karyandrew/hutchfinity/scad/gridfinity/stl/bin-5x7x5h.stl

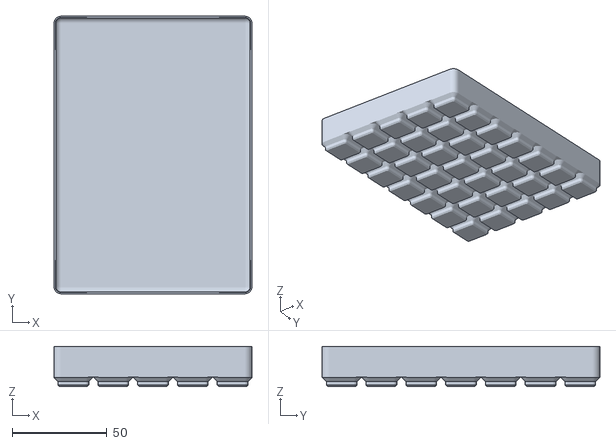
[picture p15: CAD file, 2026-06-07]
scad/gridfinity/stl/bin-5x7x5h.stl
104.5 x 146.5 x 21.2
