karyandrew/hutchfinity/scad/gridfinity/stl/bin-2x10x5h.stl

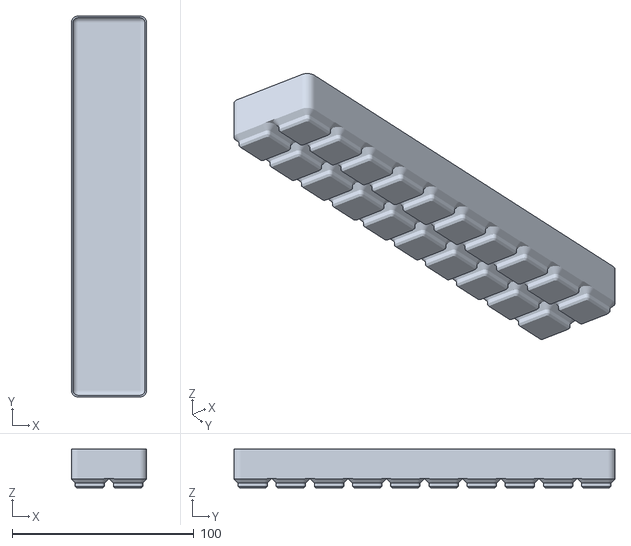
[picture p16: CAD file, 2026-06-07]
scad/gridfinity/stl/bin-2x10x5h.stl
41.5 x 209.5 x 21.2
