karyandrew/hutchfinity/scad/gridfinity/stl/bin-2x8x20h.stl

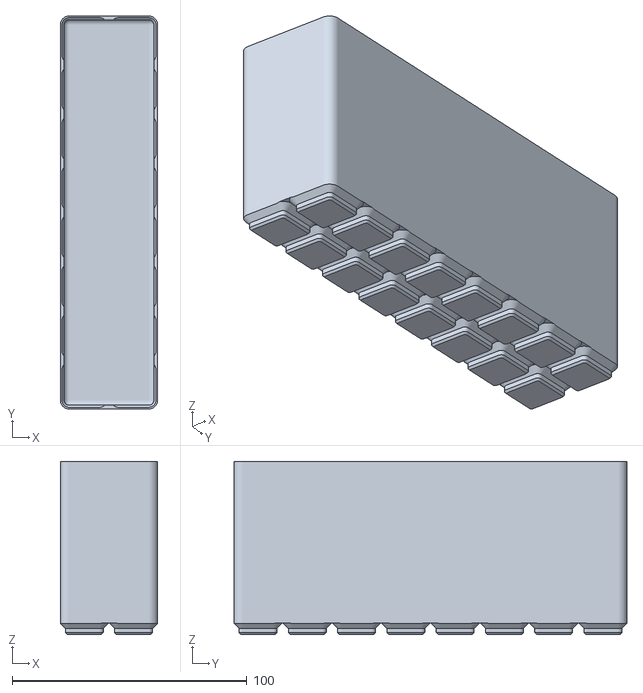
[picture p17: CAD file, 2026-06-07]
scad/gridfinity/stl/bin-2x8x20h.stl
41.5 x 167.5 x 73.7
