karyandrew/hutchfinity/scad/gridfinity/stl/bin-2x3x5h.stl

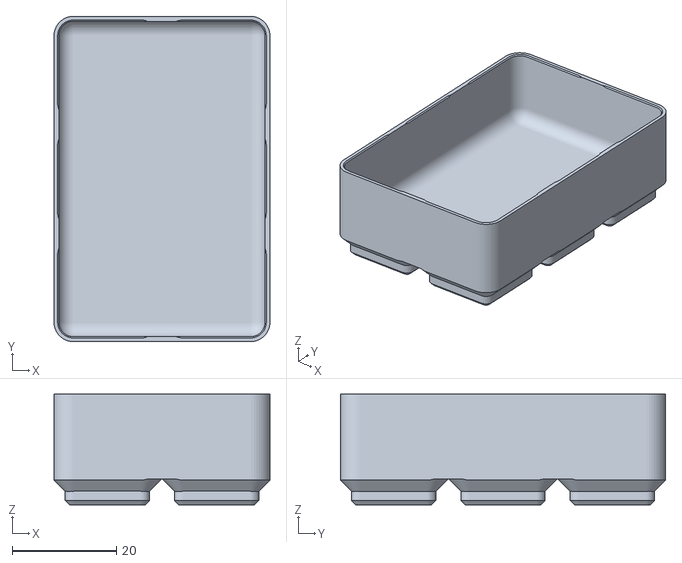
[picture p18: CAD file, 2026-06-07]
scad/gridfinity/stl/bin-2x3x5h.stl
41.5 x 62.5 x 21.2
