karyandrew/hutchfinity/scad/gridfinity/stl/bin-4x8x10h.stl

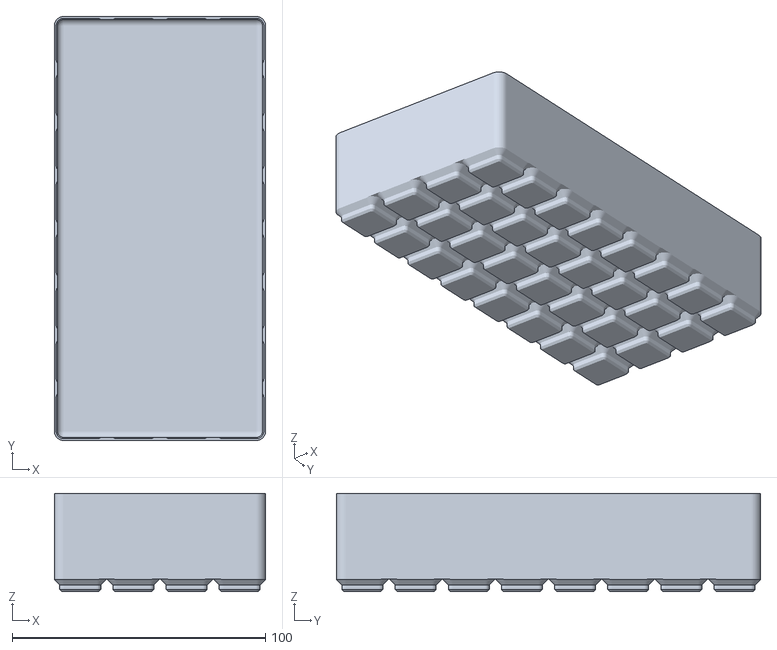
[picture p19: CAD file, 2026-06-07]
scad/gridfinity/stl/bin-4x8x10h.stl
83.5 x 167.5 x 38.7
