karyandrew/hutchfinity/scad/gridfinity/stl/bin-3x10x5h.stl

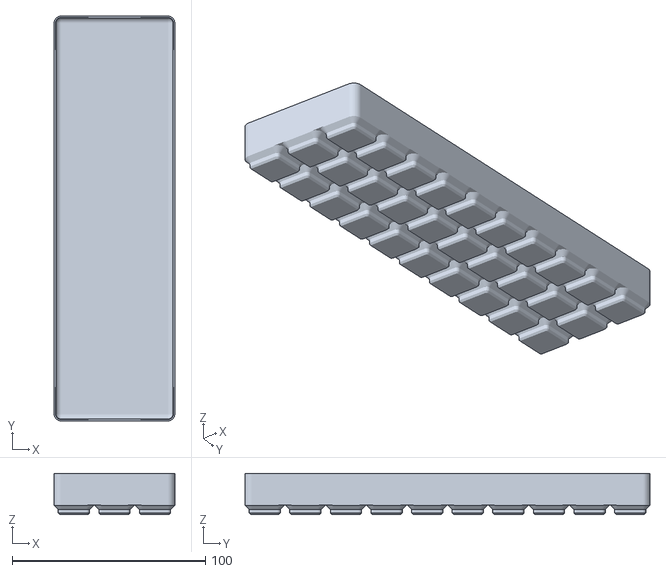
[picture p20: CAD file, 2026-06-07]
scad/gridfinity/stl/bin-3x10x5h.stl
62.5 x 209.5 x 21.2
