karyandrew/hutchfinity/scad/gridfinity/stl/bin-3x7x20h.stl

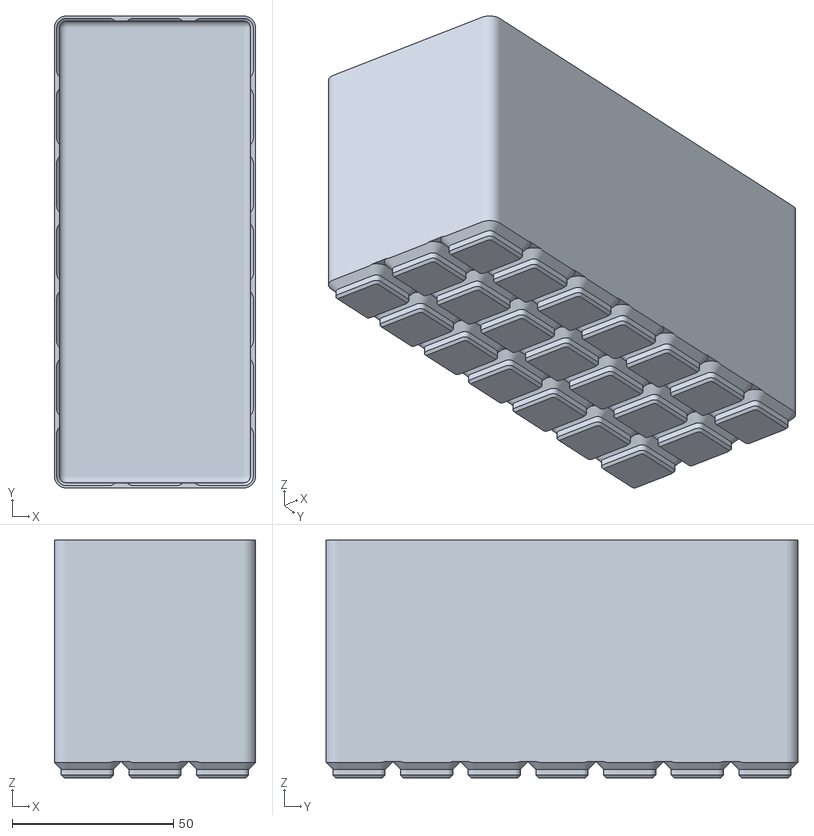
[picture p21: CAD file, 2026-06-07]
scad/gridfinity/stl/bin-3x7x20h.stl
62.5 x 146.5 x 73.7
