karyandrew/hutchfinity/scad/gridfinity/stl/bin-3x7x10h.stl

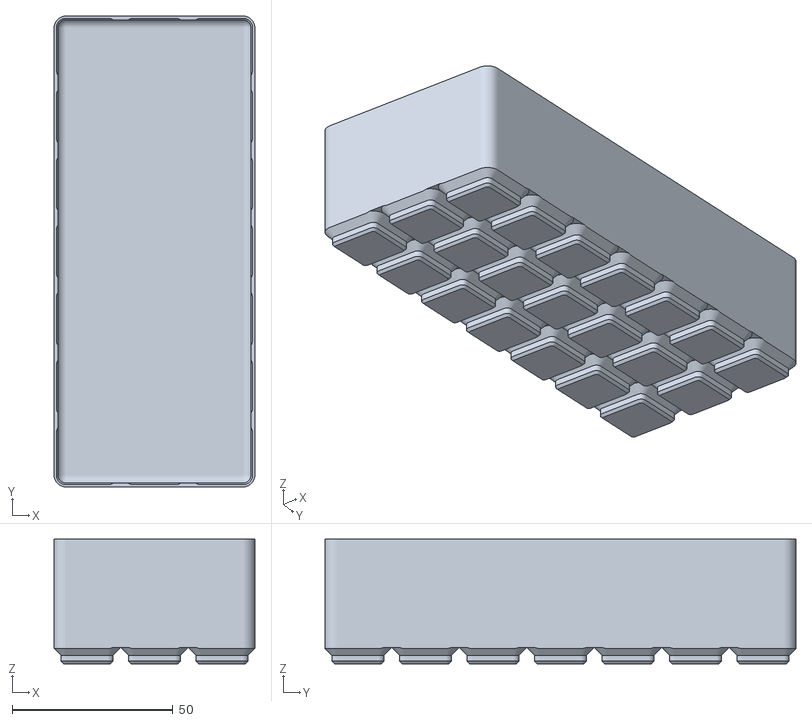
[picture p22: CAD file, 2026-06-07]
scad/gridfinity/stl/bin-3x7x10h.stl
62.5 x 146.5 x 38.7
