karyandrew/hutchfinity/scad/gridfinity/stl/baseplate-regular-cropped.stl

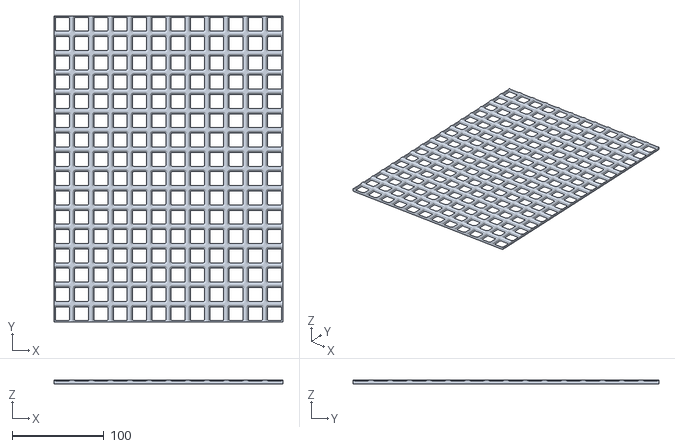
[picture p23: CAD file, 2026-06-07]
scad/gridfinity/stl/baseplate-regular-cropped.stl
249.0 x 333.0 x 4.00
