karyandrew/hutchfinity/scad/gridfinity/stl/tub-mini-10u.stl

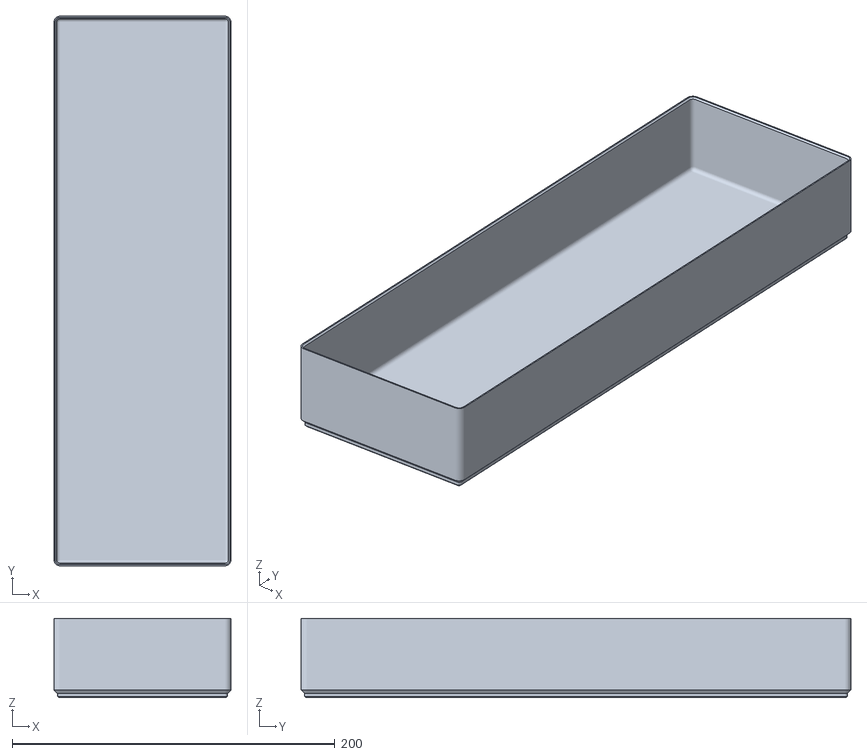
[picture p24: CAD file, 2026-06-07]
scad/gridfinity/stl/tub-mini-10u.stl
109.7 x 340.7 x 49.2
