karyandrew/hutchfinity/scad/gridfinity/stl/bin-3x6x10h.stl

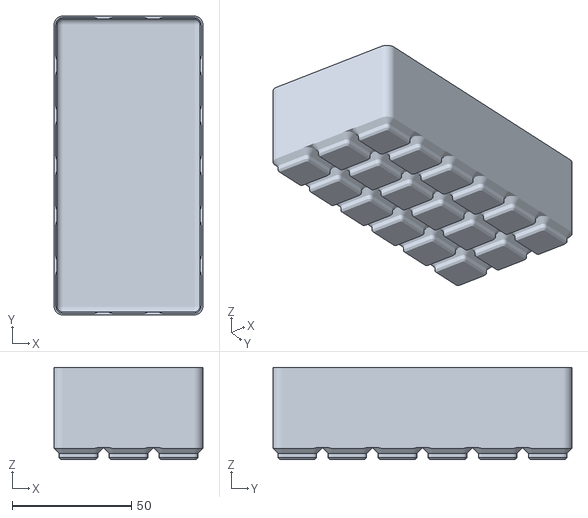
[picture p25: CAD file, 2026-06-07]
scad/gridfinity/stl/bin-3x6x10h.stl
62.5 x 125.5 x 38.7
