karyandrew/hutchfinity/scad/gridfinity/stl/bin-3x4x10h.stl

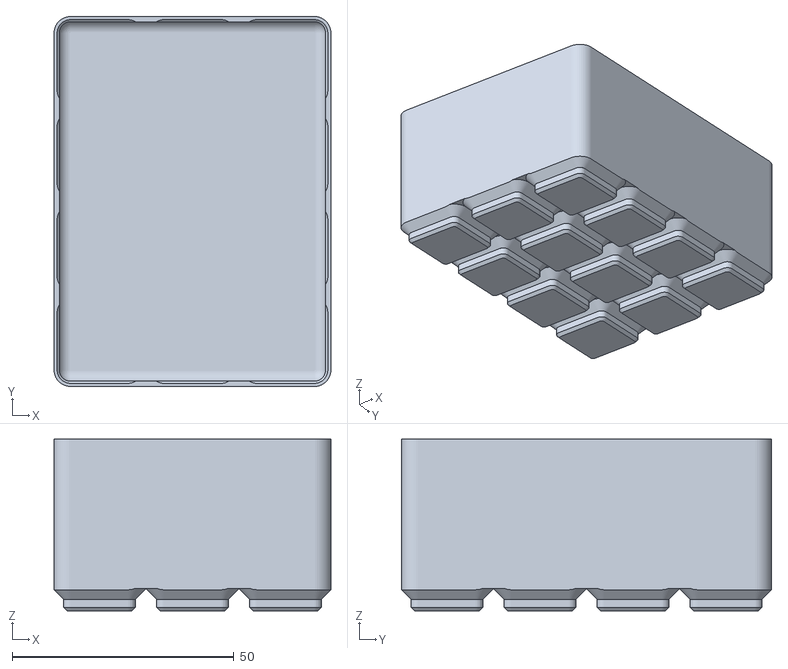
[picture p26: CAD file, 2026-06-07]
scad/gridfinity/stl/bin-3x4x10h.stl
62.5 x 83.5 x 38.7
