karyandrew/hutchfinity/scad/gridfinity/stl/bin-3x5x20h.stl

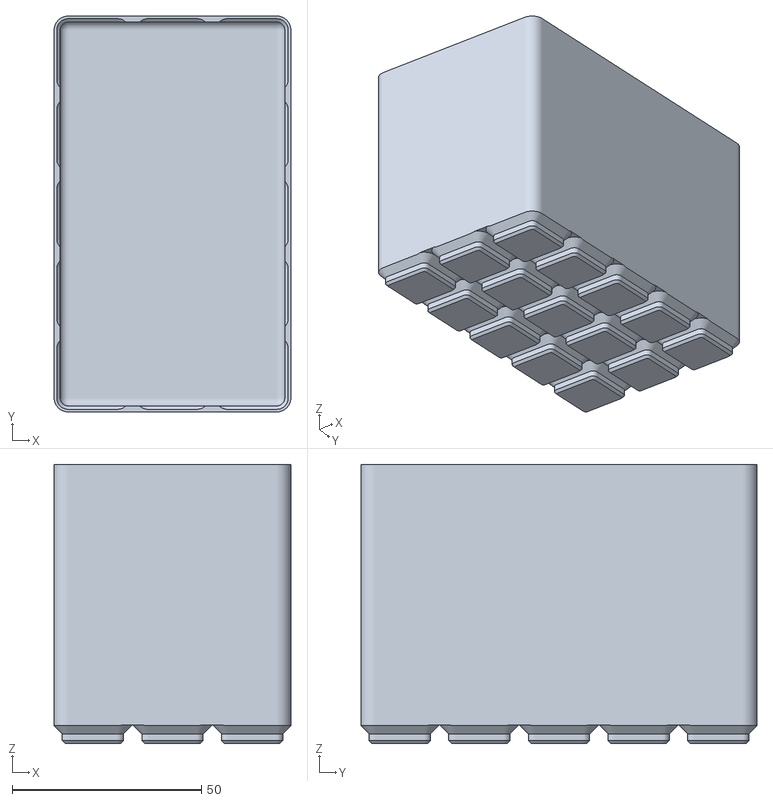
[picture p27: CAD file, 2026-06-07]
scad/gridfinity/stl/bin-3x5x20h.stl
62.5 x 104.5 x 73.7
