karyandrew/hutchfinity/scad/gridfinity/stl/bin-5x10x10h.stl

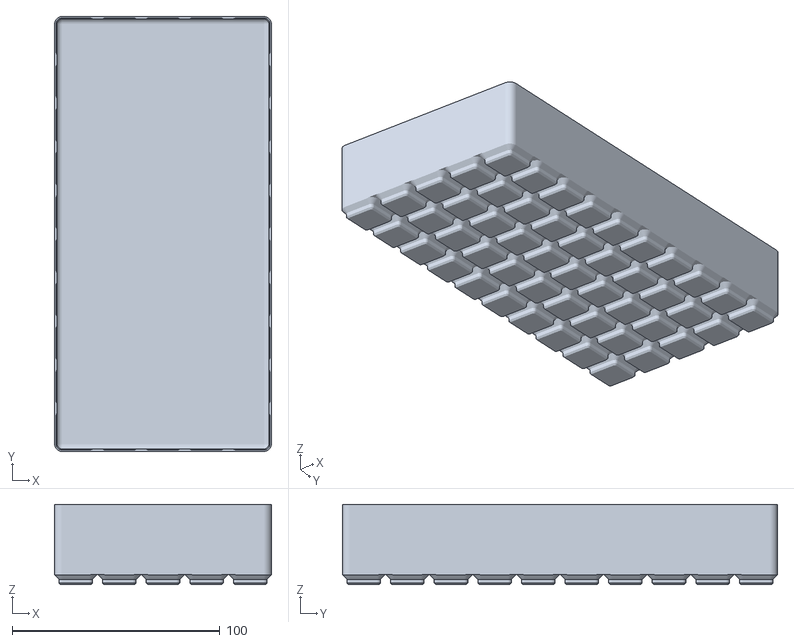
[picture p28: CAD file, 2026-06-07]
scad/gridfinity/stl/bin-5x10x10h.stl
104.5 x 209.5 x 38.7
