karyandrew/hutchfinity/scad/gridfinity/stl/bin-1x8x5h.stl

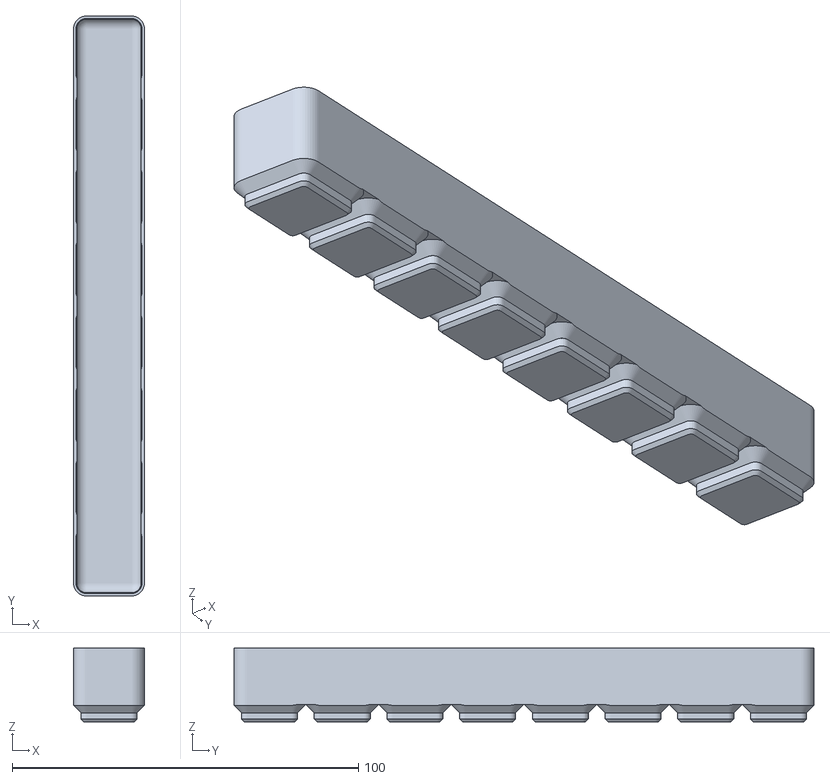
[picture p29: CAD file, 2026-06-07]
scad/gridfinity/stl/bin-1x8x5h.stl
20.5 x 167.5 x 21.2
