karyandrew/hutchfinity/scad/gridfinity/stl/bin-5x8x10h.stl

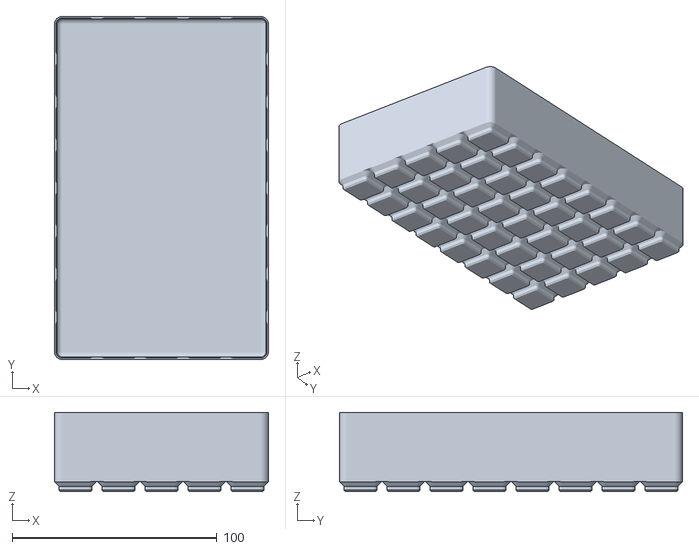
[picture p30: CAD file, 2026-06-07]
scad/gridfinity/stl/bin-5x8x10h.stl
104.5 x 167.5 x 38.7
