karyandrew/hutchfinity/scad/gridfinity/stl/bin-1x9x20h.stl

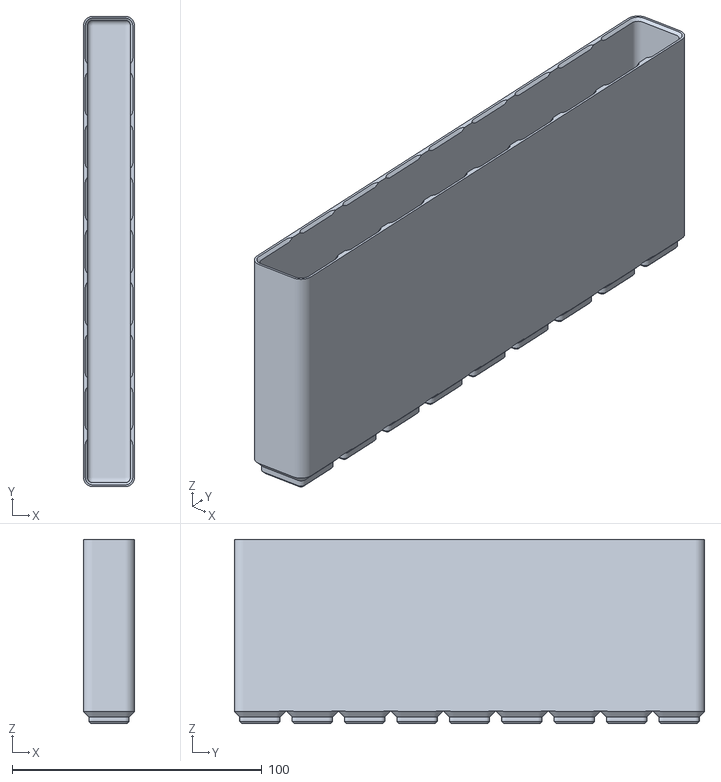
[picture p31: CAD file, 2026-06-07]
scad/gridfinity/stl/bin-1x9x20h.stl
20.5 x 188.5 x 73.7
