karyandrew/hutchfinity/scad/gridfinity/stl/bin-1x10x10h.stl

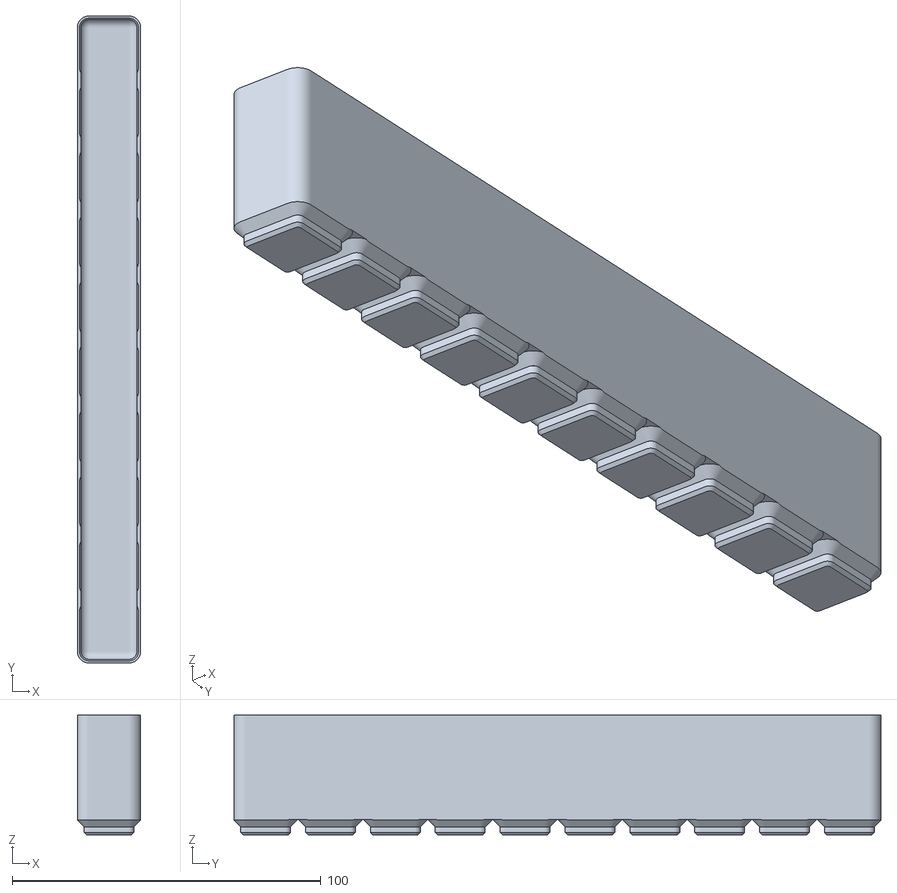
[picture p32: CAD file, 2026-06-07]
scad/gridfinity/stl/bin-1x10x10h.stl
20.5 x 209.5 x 38.7
