karyandrew/hutchfinity/scad/gridfinity/stl/tub-regular-10u.stl

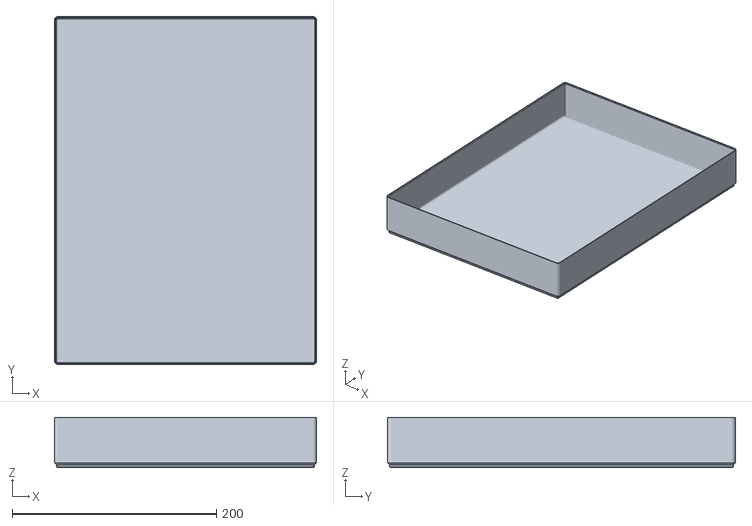
[picture p33: CAD file, 2026-06-07]
scad/gridfinity/stl/tub-regular-10u.stl
256.7 x 340.7 x 49.2
