karyandrew/hutchfinity/scad/gridfinity/stl/bin-5x10x20h.stl

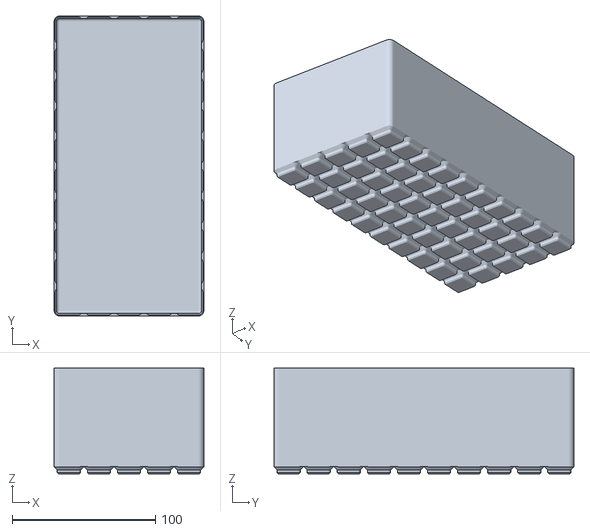
[picture p34: CAD file, 2026-06-07]
scad/gridfinity/stl/bin-5x10x20h.stl
104.5 x 209.5 x 73.7
