karyandrew/hutchfinity/scad/gridfinity/stl/bin-1x6x20h.stl

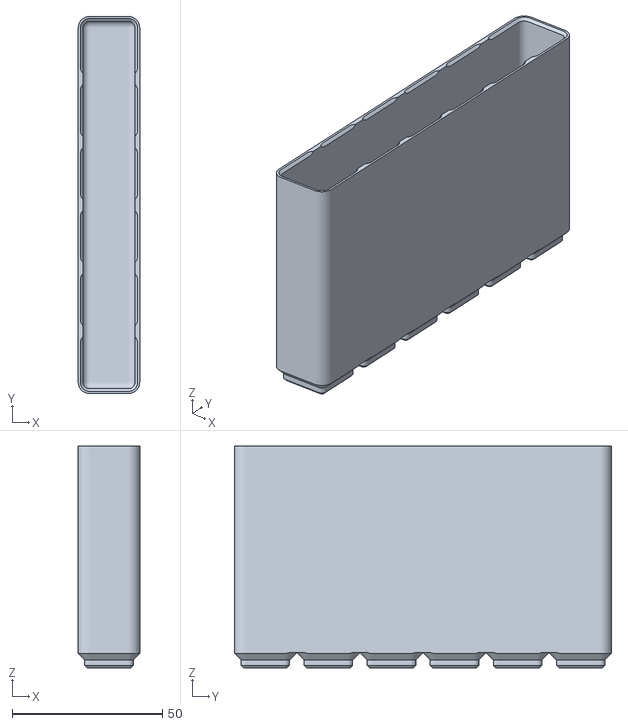
[picture p35: CAD file, 2026-06-07]
scad/gridfinity/stl/bin-1x6x20h.stl
20.5 x 125.5 x 73.7
