karyandrew/hutchfinity/scad/gridfinity/stl/bin-5x8x20h.stl

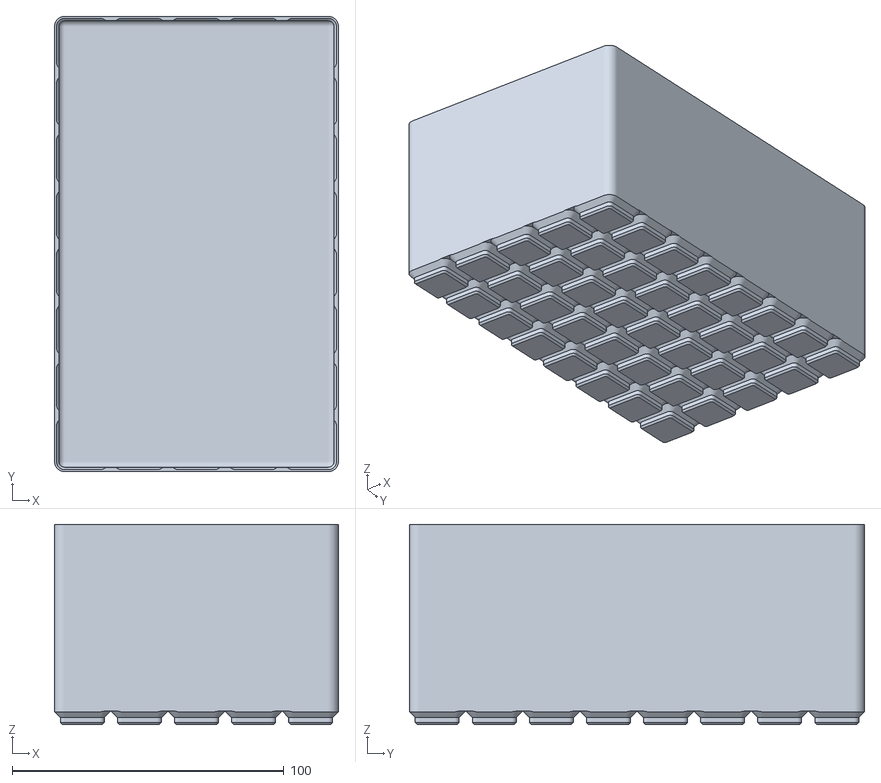
[picture p36: CAD file, 2026-06-07]
scad/gridfinity/stl/bin-5x8x20h.stl
104.5 x 167.5 x 73.7
