karyandrew/hutchfinity/scad/gridfinity/stl/bin-4x10x5h.stl

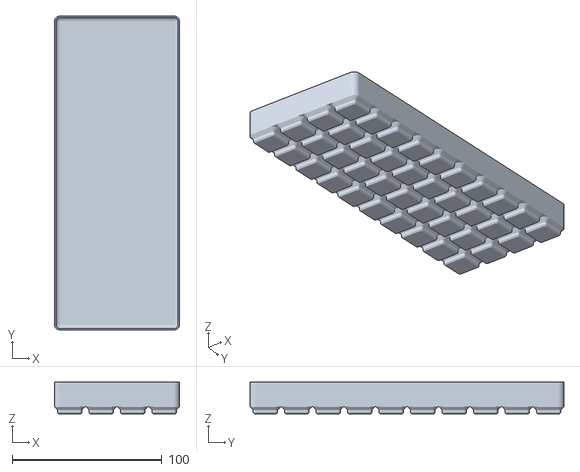
[picture p37: CAD file, 2026-06-07]
scad/gridfinity/stl/bin-4x10x5h.stl
83.5 x 209.5 x 21.2
