karyandrew/hutchfinity/scad/gridfinity/stl/tub-mega-10u.stl

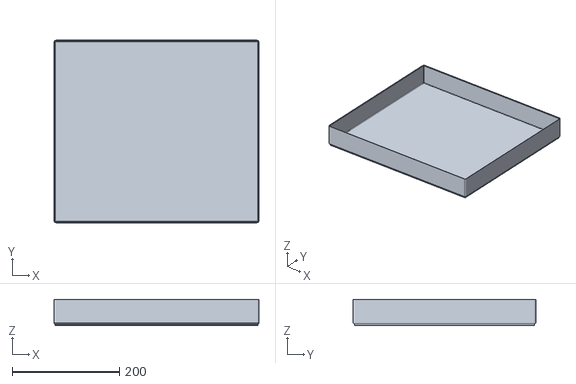
[picture p38: CAD file, 2026-06-07]
scad/gridfinity/stl/tub-mega-10u.stl
382.7 x 340.7 x 49.2
