karyandrew/hutchfinity/scad/gridfinity/stl/bin-2x7x5h.stl

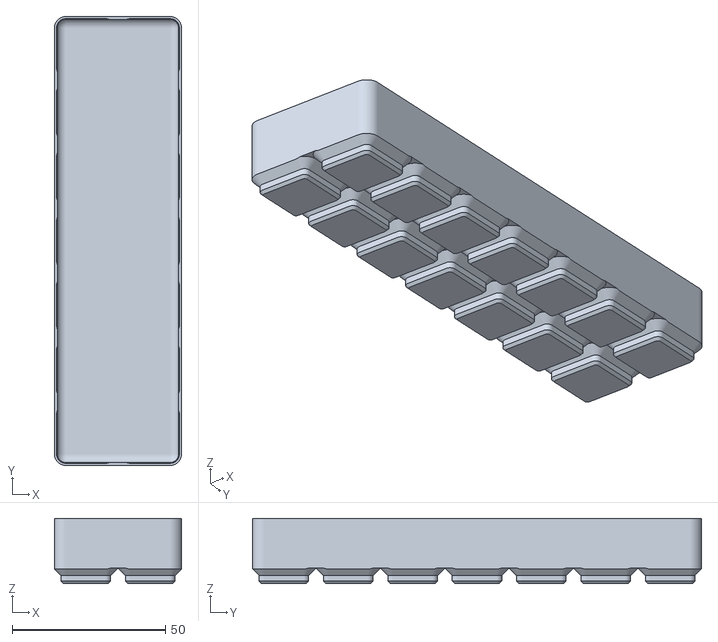
[picture p39: CAD file, 2026-06-07]
scad/gridfinity/stl/bin-2x7x5h.stl
41.5 x 146.5 x 21.2
