karyandrew/hutchfinity/scad/gridfinity/stl/bin-3x4x5h.stl

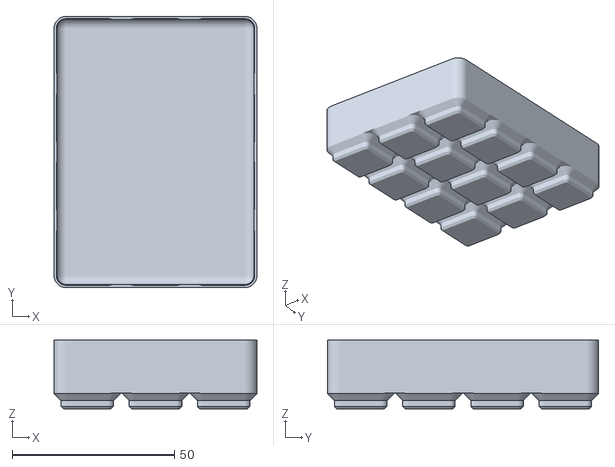
[picture p40: CAD file, 2026-06-07]
scad/gridfinity/stl/bin-3x4x5h.stl
62.5 x 83.5 x 21.2
