karyandrew/hutchfinity/scad/gridfinity/stl/bin-1x6x10h.stl

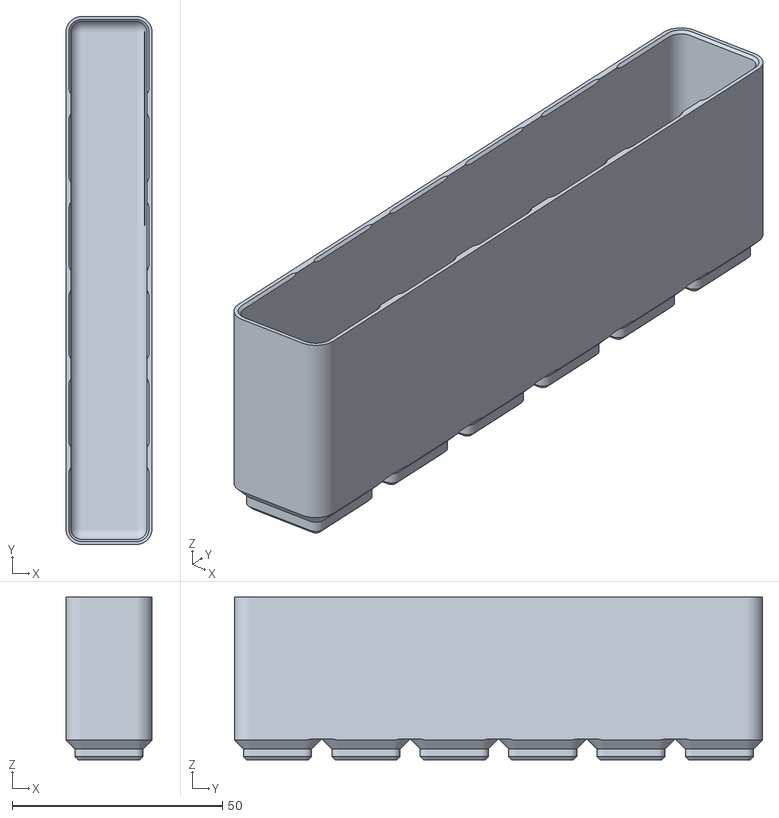
[picture p41: CAD file, 2026-06-07]
scad/gridfinity/stl/bin-1x6x10h.stl
20.5 x 125.5 x 38.7
