karyandrew/hutchfinity/scad/gridfinity/stl/bin-2x6x20h.stl

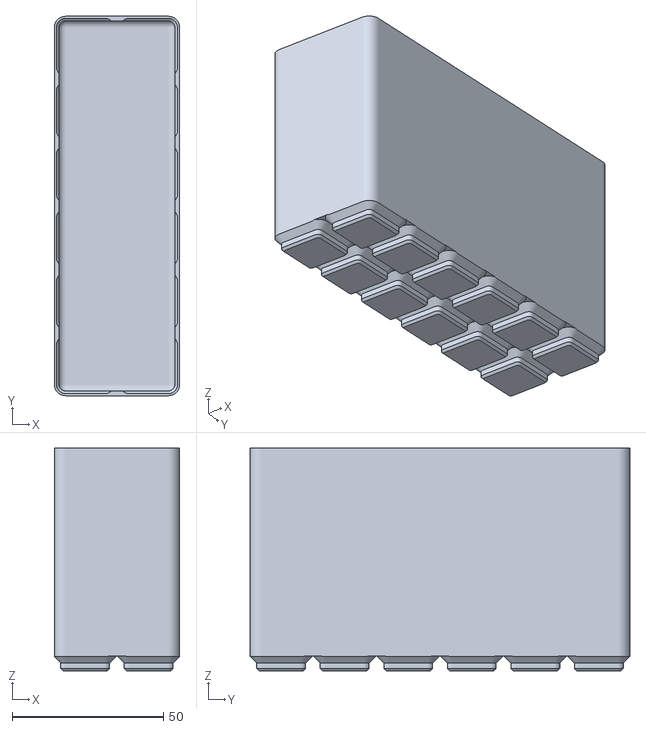
[picture p42: CAD file, 2026-06-07]
scad/gridfinity/stl/bin-2x6x20h.stl
41.5 x 125.5 x 73.7
