karyandrew/hutchfinity/scad/gridfinity/stl/bin-4x8x20h.stl

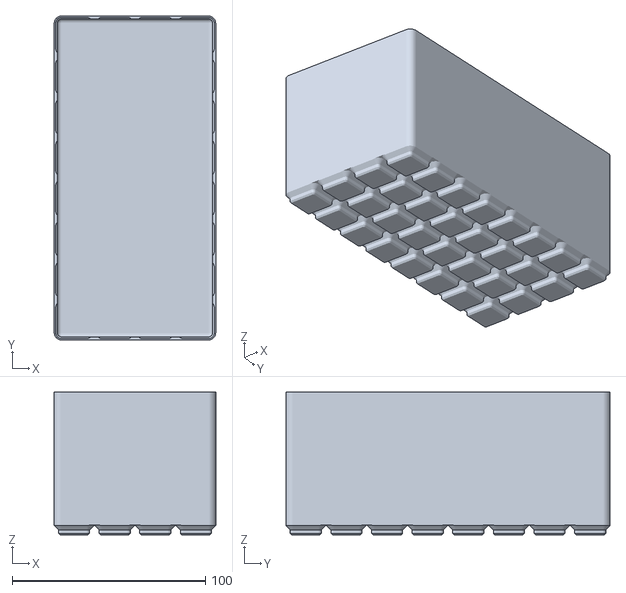
[picture p43: CAD file, 2026-06-07]
scad/gridfinity/stl/bin-4x8x20h.stl
83.5 x 167.5 x 73.7
