karyandrew/hutchfinity/scad/gridfinity/stl/bin-3x6x5h.stl

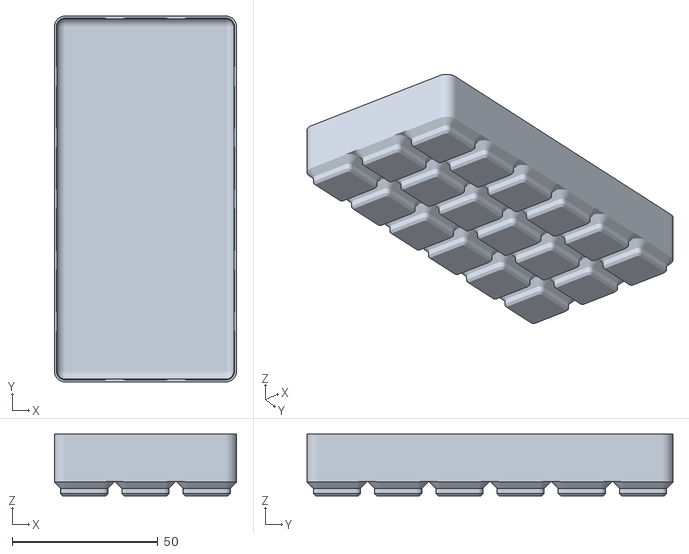
[picture p44: CAD file, 2026-06-07]
scad/gridfinity/stl/bin-3x6x5h.stl
62.5 x 125.5 x 21.2
