karyandrew/hutchfinity/scad/gridfinity/stl/bin-3x8x20h.stl

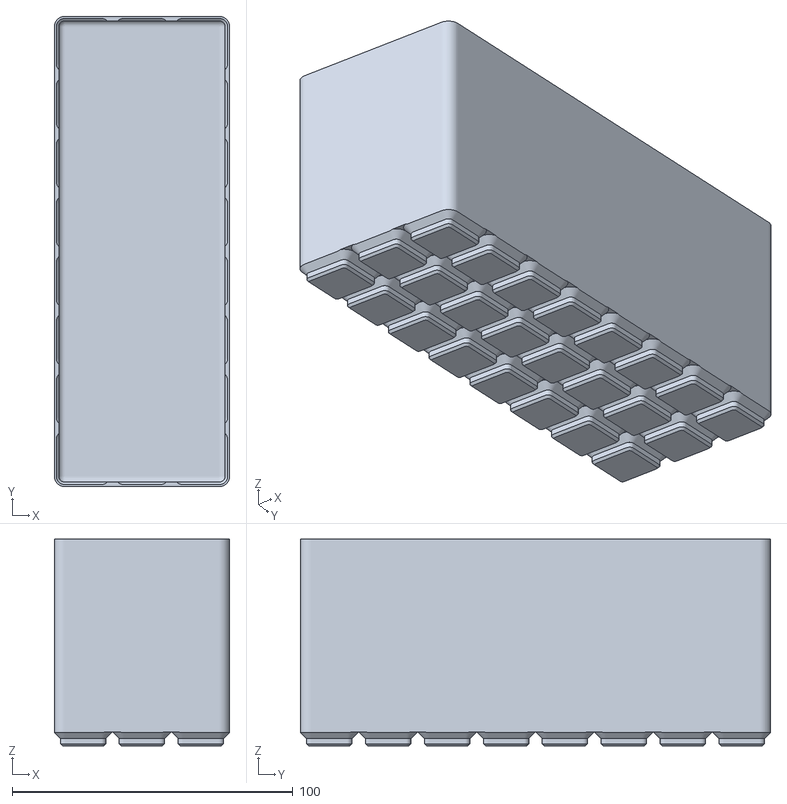
[picture p45: CAD file, 2026-06-07]
scad/gridfinity/stl/bin-3x8x20h.stl
62.5 x 167.5 x 73.7
