karyandrew/hutchfinity/scad/gridfinity/stl/bin-2x9x5h.stl

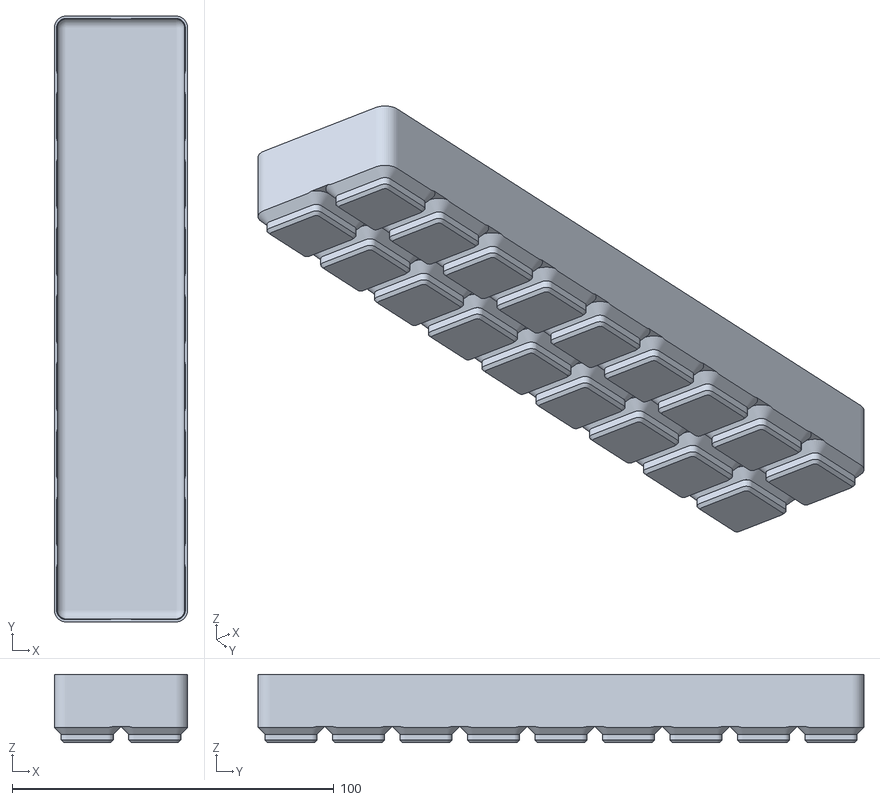
[picture p46: CAD file, 2026-06-07]
scad/gridfinity/stl/bin-2x9x5h.stl
41.5 x 188.5 x 21.2
