karyandrew/hutchfinity/scad/gridfinity/stl/bin-4x4x5h.stl

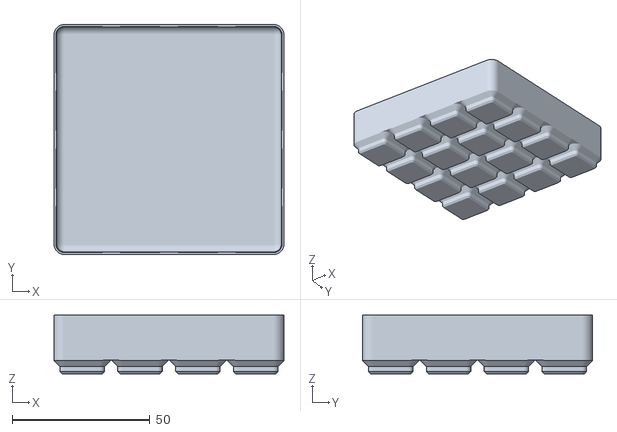
[picture p47: CAD file, 2026-06-07]
scad/gridfinity/stl/bin-4x4x5h.stl
83.5 x 83.5 x 21.2
