karyandrew/hutchfinity/scad/gridfinity/stl/bin-3x10x10h.stl

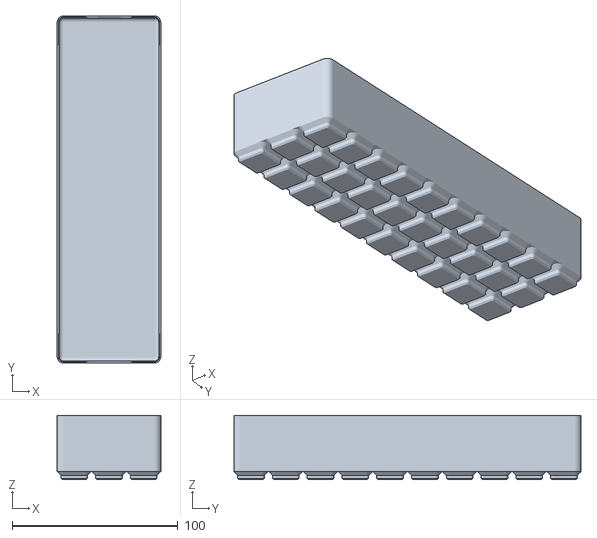
[picture p48: CAD file, 2026-06-07]
scad/gridfinity/stl/bin-3x10x10h.stl
62.5 x 209.5 x 38.7
