karyandrew/hutchfinity/scad/gridfinity/stl/bin-2x6x5h.stl

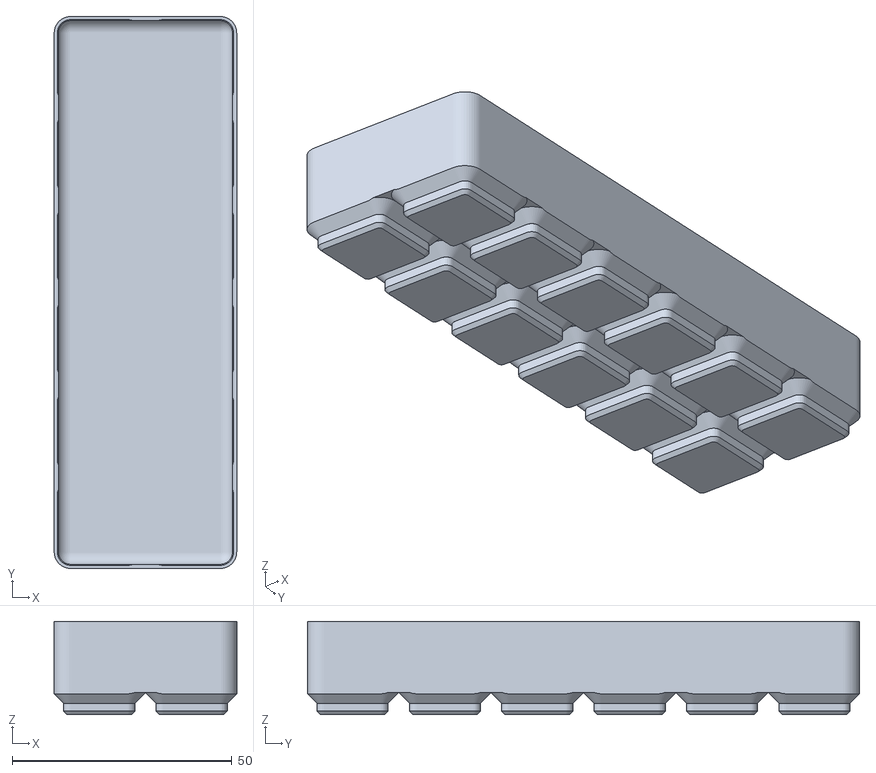
[picture p49: CAD file, 2026-06-07]
scad/gridfinity/stl/bin-2x6x5h.stl
41.5 x 125.5 x 21.2
