karyandrew/hutchfinity/scad/gridfinity/stl/bin-1x4x5h.stl

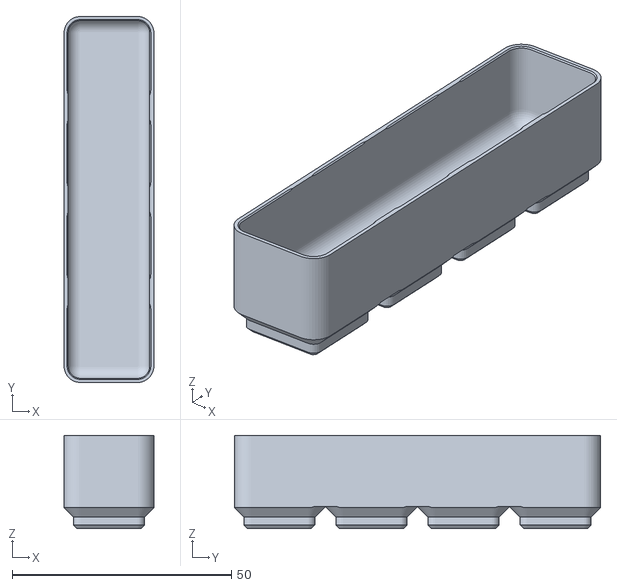
[picture p50: CAD file, 2026-06-07]
scad/gridfinity/stl/bin-1x4x5h.stl
20.5 x 83.5 x 21.2
