karyandrew/hutchfinity/scad/gridfinity/stl/bin-4x10x10h.stl

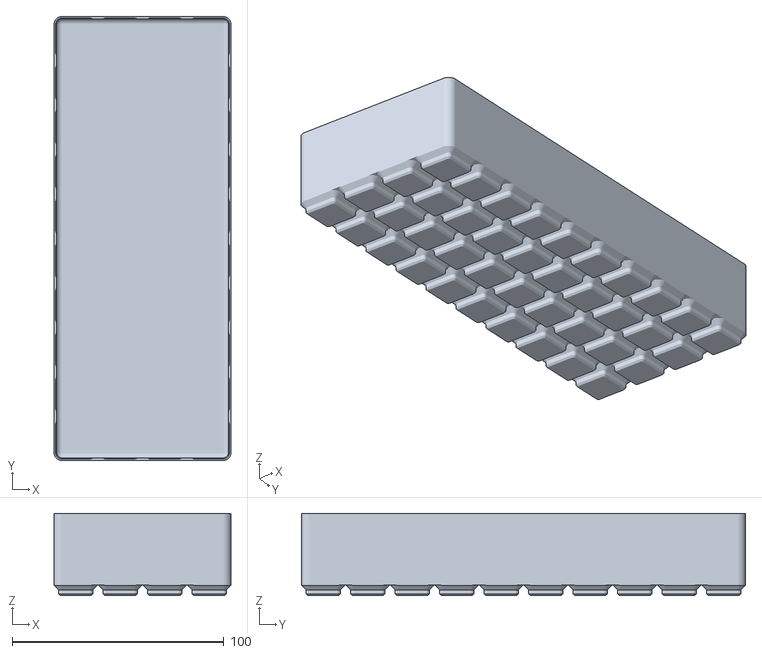
[picture p51: CAD file, 2026-06-07]
scad/gridfinity/stl/bin-4x10x10h.stl
83.5 x 209.5 x 38.7
