karyandrew/hutchfinity/scad/gridfinity/stl/bin-2x8x10h.stl

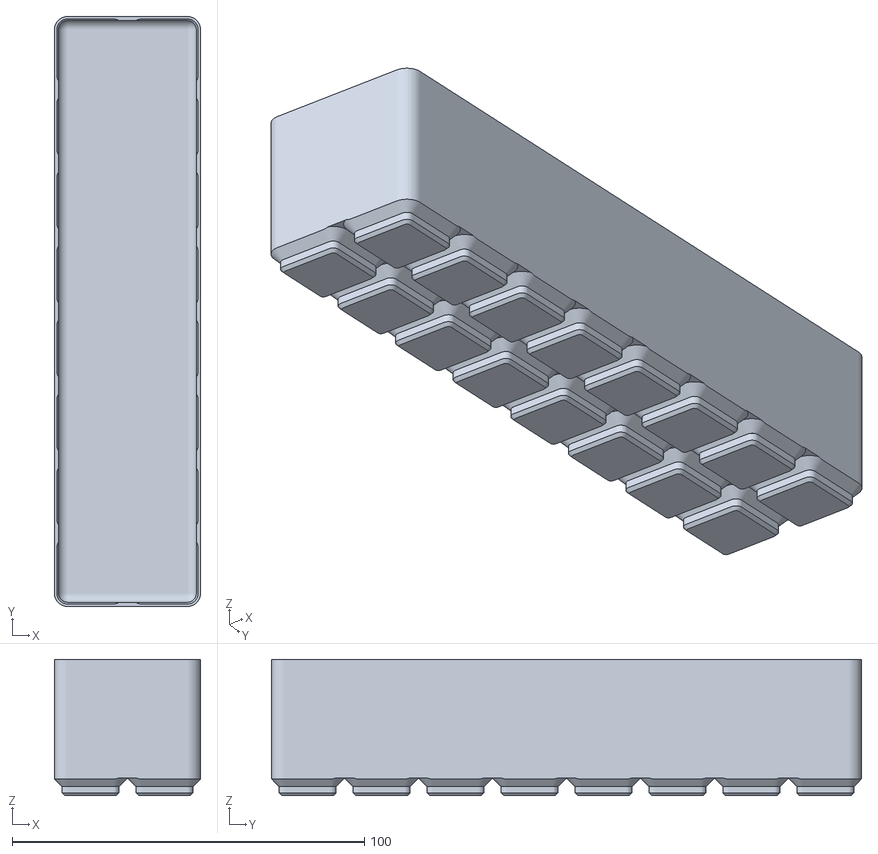
[picture p52: CAD file, 2026-06-07]
scad/gridfinity/stl/bin-2x8x10h.stl
41.5 x 167.5 x 38.7
