karyandrew/hutchfinity/scad/gridfinity/stl/bin-5x5x5h.stl

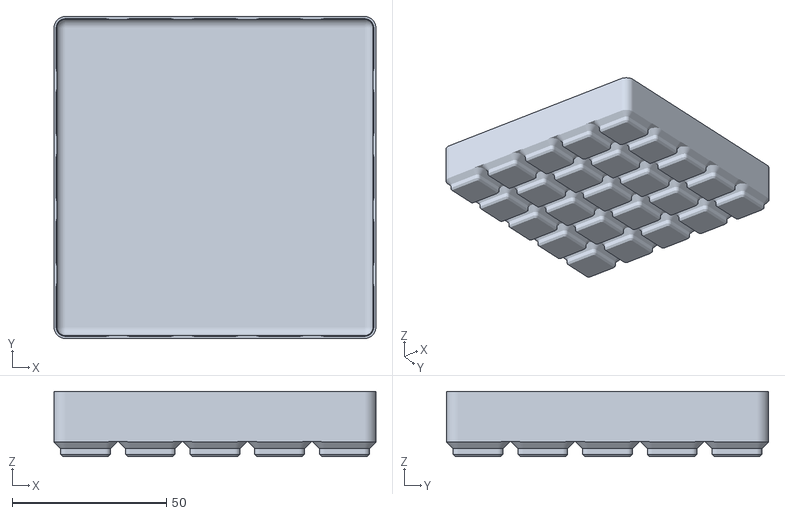
[picture p53: CAD file, 2026-06-07]
scad/gridfinity/stl/bin-5x5x5h.stl
104.5 x 104.5 x 21.2
