karyandrew/hutchfinity/scad/gridfinity/stl/bin-5x6x5h.stl

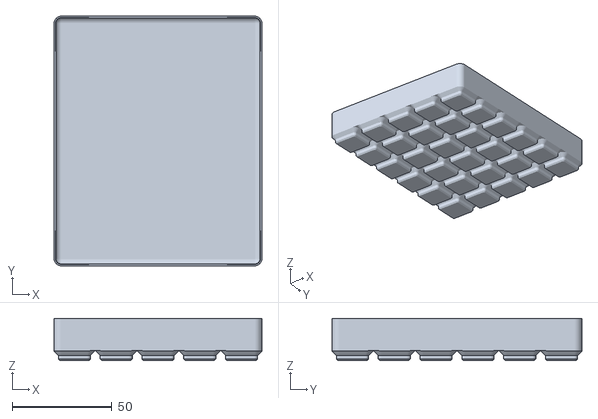
[picture p54: CAD file, 2026-06-07]
scad/gridfinity/stl/bin-5x6x5h.stl
104.5 x 125.5 x 21.2
