karyandrew/hutchfinity/scad/gridfinity/stl/bin-1x2x5h.stl

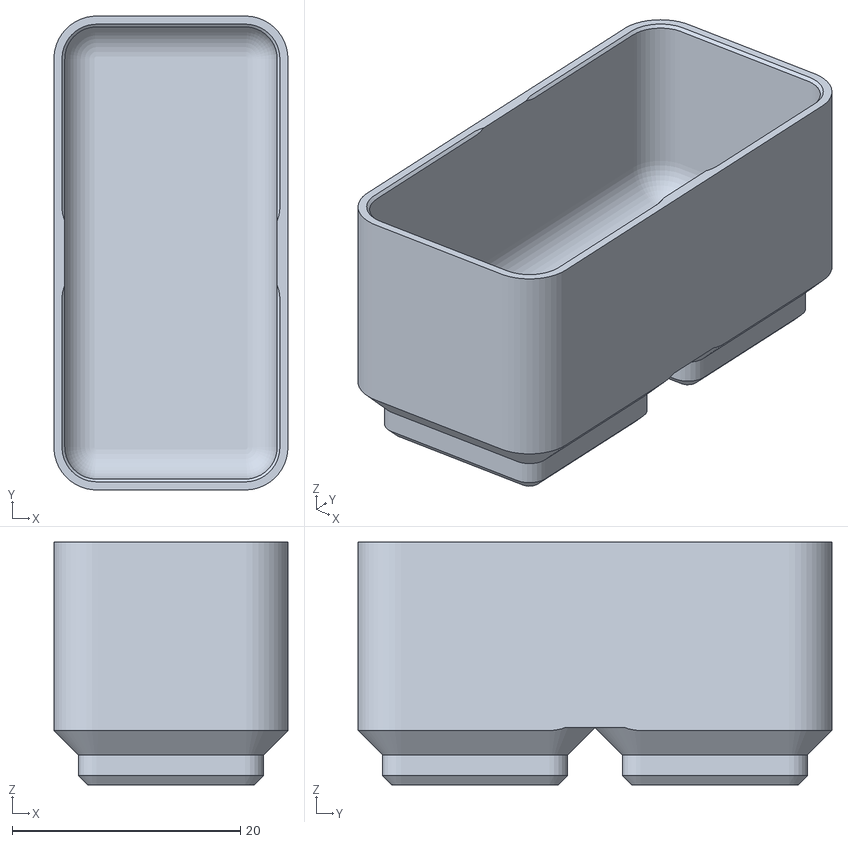
[picture p55: CAD file, 2026-06-07]
scad/gridfinity/stl/bin-1x2x5h.stl
20.5 x 41.5 x 21.2
