karyandrew/hutchfinity/scad/gridfinity/stl/bin-4x7x5h.stl

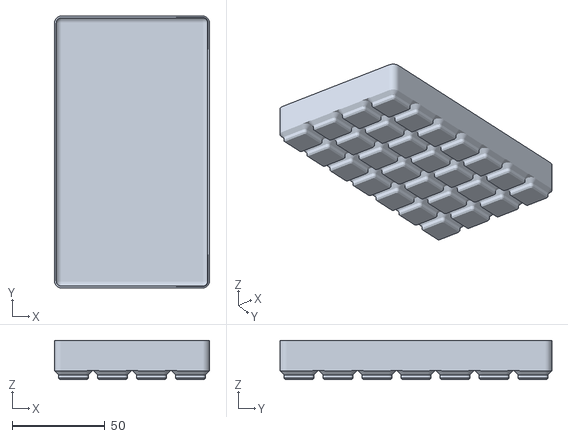
[picture p56: CAD file, 2026-06-07]
scad/gridfinity/stl/bin-4x7x5h.stl
83.5 x 146.5 x 21.2
