karyandrew/hutchfinity/scad/gridfinity/stl/bin-3x5x5h.stl

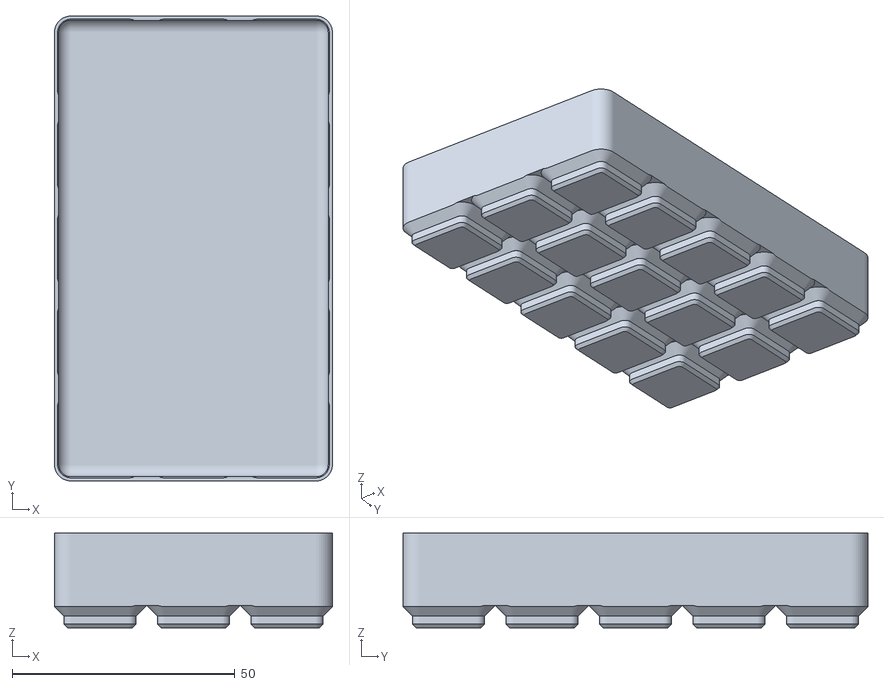
[picture p57: CAD file, 2026-06-07]
scad/gridfinity/stl/bin-3x5x5h.stl
62.5 x 104.5 x 21.2
