karyandrew/hutchfinity/scad/gridfinity/stl/bin-2x8x5h.stl

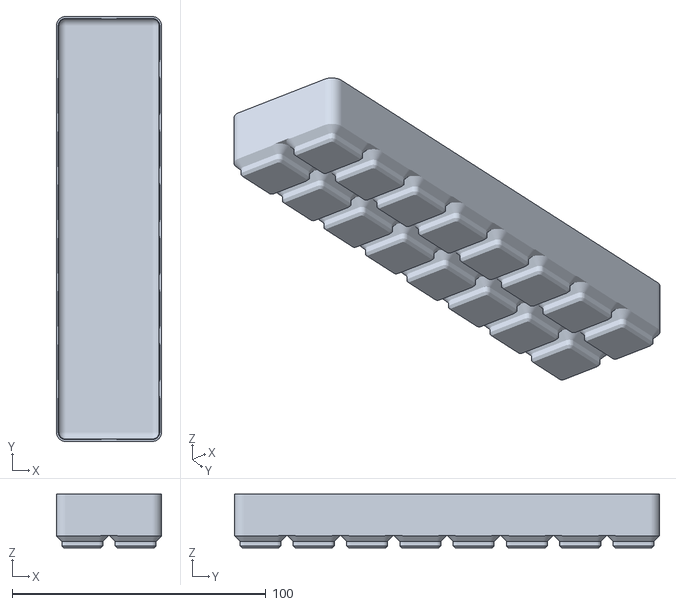
[picture p58: CAD file, 2026-06-07]
scad/gridfinity/stl/bin-2x8x5h.stl
41.5 x 167.5 x 21.2
