karyandrew/hutchfinity/scad/gridfinity/stl/bin-1x2x10h.stl

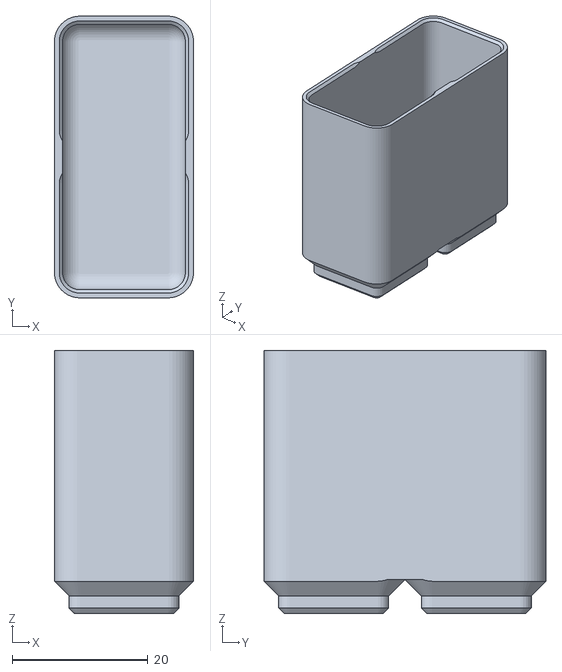
[picture p59: CAD file, 2026-06-07]
scad/gridfinity/stl/bin-1x2x10h.stl
20.5 x 41.5 x 38.7
