karyandrew/hutchfinity/scad/gridfinity/stl/bin-4x9x5h.stl

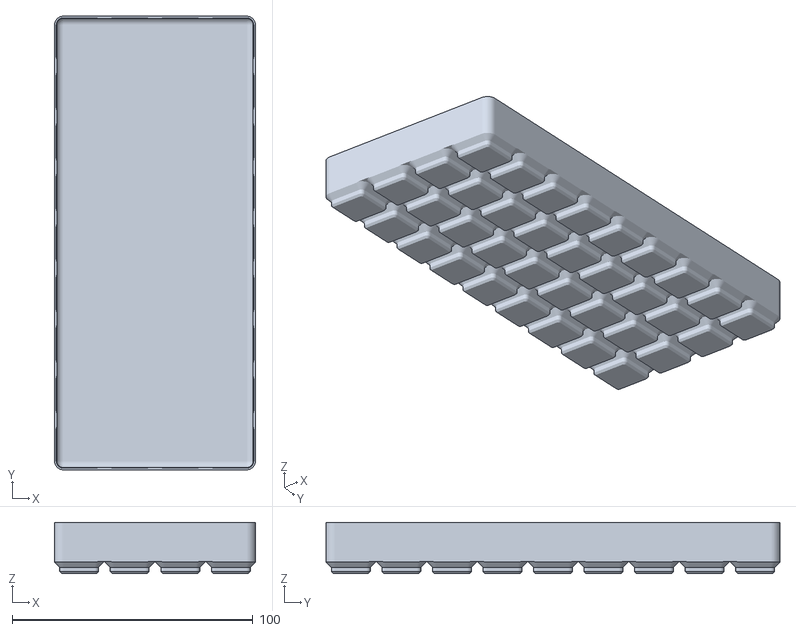
[picture p60: CAD file, 2026-06-07]
scad/gridfinity/stl/bin-4x9x5h.stl
83.5 x 188.5 x 21.2
