karyandrew/hutchfinity/scad/gridfinity/stl/bin-2x4x5h.stl

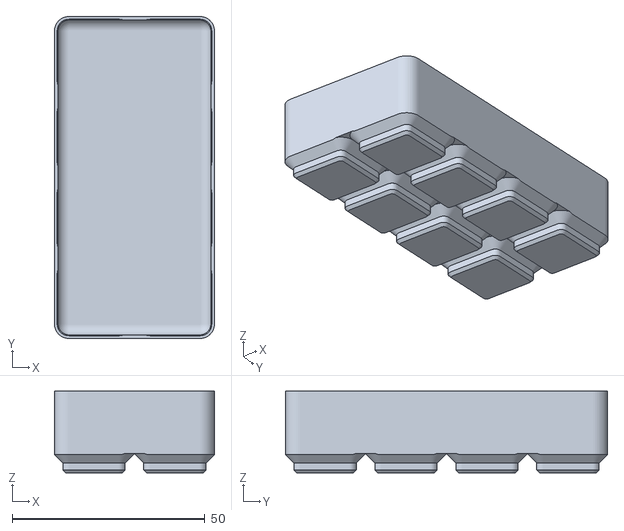
[picture p61: CAD file, 2026-06-07]
scad/gridfinity/stl/bin-2x4x5h.stl
41.5 x 83.5 x 21.2
