karyandrew/hutchfinity/scad/gridfinity/stl/bin-5x5x10h.stl

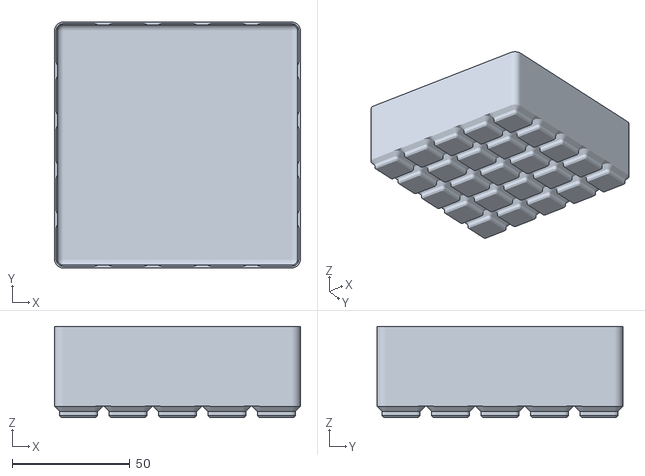
[picture p62: CAD file, 2026-06-07]
scad/gridfinity/stl/bin-5x5x10h.stl
104.5 x 104.5 x 38.7
