karyandrew/hutchfinity/scad/gridfinity/stl/bin-1x7x5h.stl

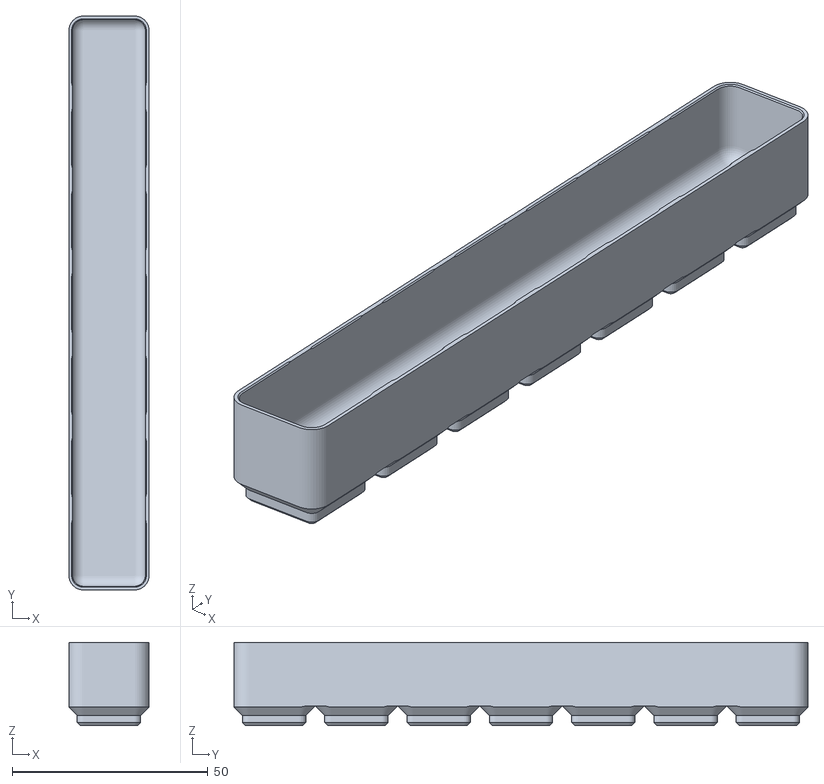
[picture p63: CAD file, 2026-06-07]
scad/gridfinity/stl/bin-1x7x5h.stl
20.5 x 146.5 x 21.2
