karyandrew/hutchfinity/scad/gridfinity/stl/bin-1x4x20h.stl

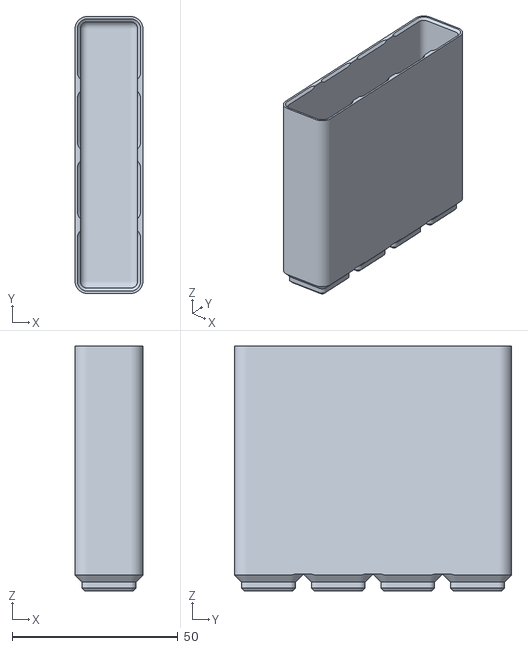
[picture p64: CAD file, 2026-06-07]
scad/gridfinity/stl/bin-1x4x20h.stl
20.5 x 83.5 x 73.7
