karyandrew/hutchfinity/scad/gridfinity/stl/bin-4x6x20h.stl

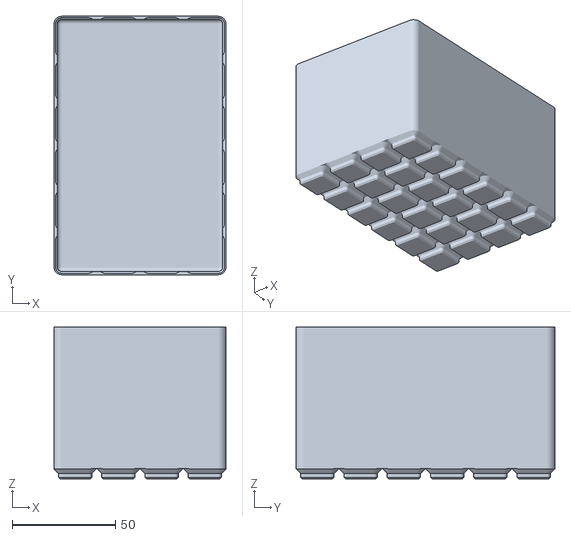
[picture p65: CAD file, 2026-06-07]
scad/gridfinity/stl/bin-4x6x20h.stl
83.5 x 125.5 x 73.7
