karyandrew/hutchfinity/scad/gridfinity/stl/bin-5x7x20h.stl

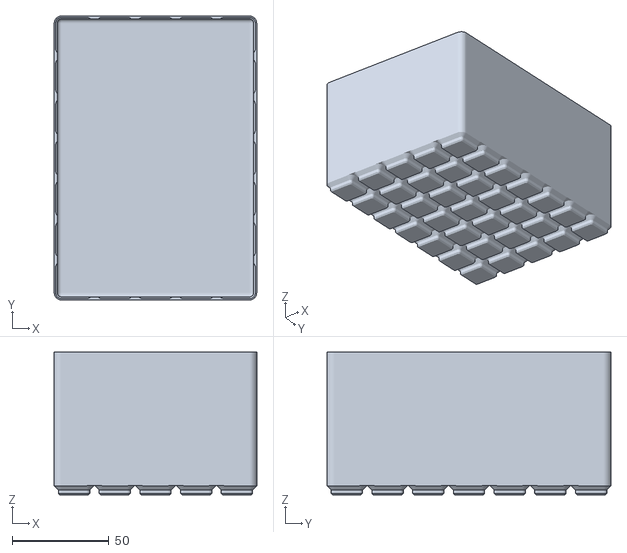
[picture p66: CAD file, 2026-06-07]
scad/gridfinity/stl/bin-5x7x20h.stl
104.5 x 146.5 x 73.7
