karyandrew/hutchfinity/scad/gridfinity/stl/bin-4x7x10h.stl

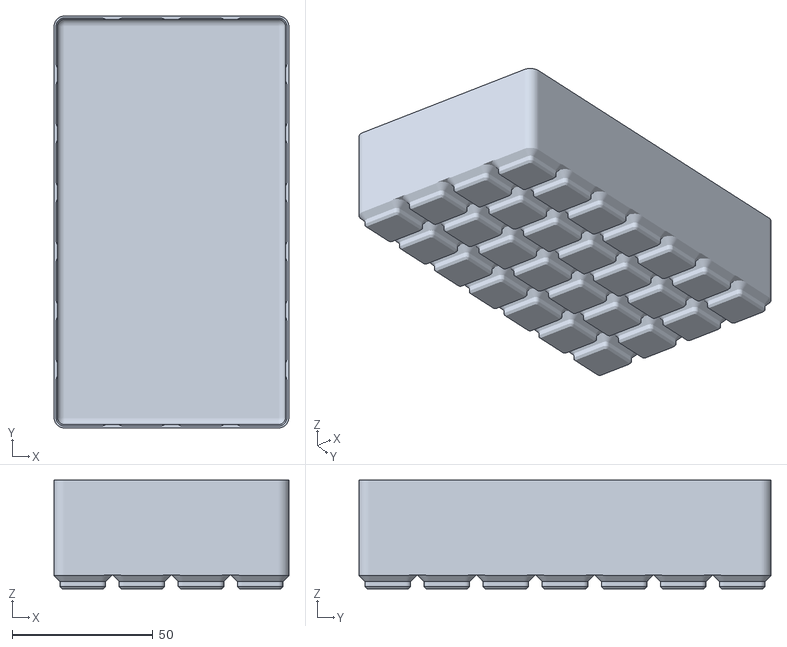
[picture p67: CAD file, 2026-06-07]
scad/gridfinity/stl/bin-4x7x10h.stl
83.5 x 146.5 x 38.7
