karyandrew/hutchfinity/scad/gridfinity/stl/bin-3x3x20h.stl

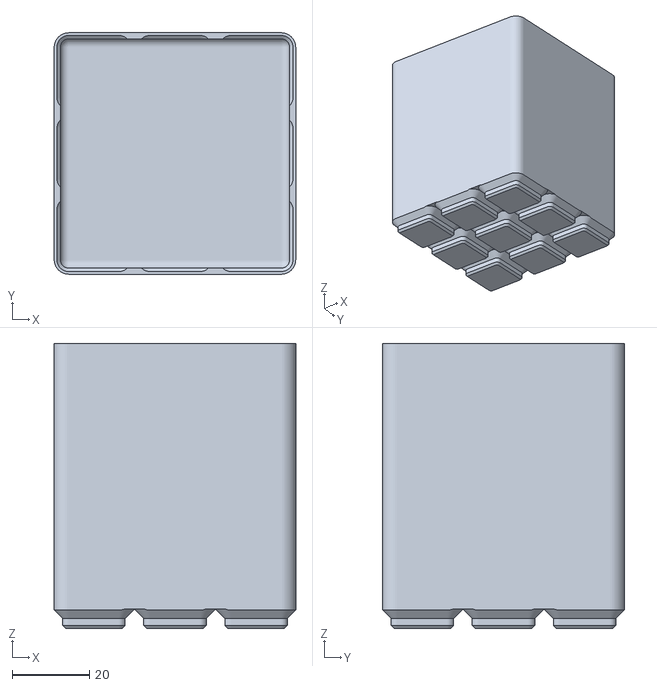
[picture p68: CAD file, 2026-06-07]
scad/gridfinity/stl/bin-3x3x20h.stl
62.5 x 62.5 x 73.7
