karyandrew/hutchfinity/scad/gridfinity/stl/bin-1x8x10h.stl

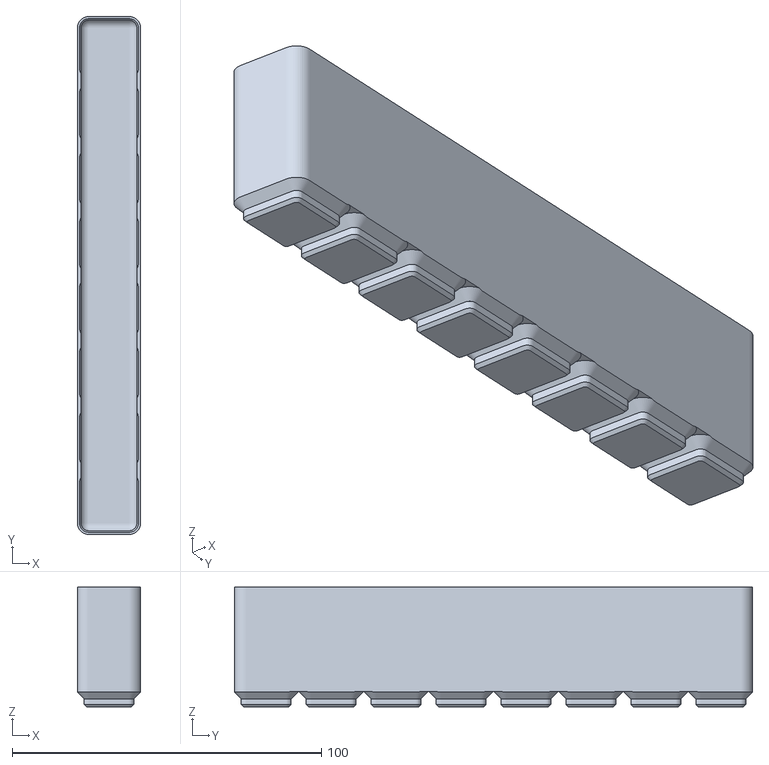
[picture p69: CAD file, 2026-06-07]
scad/gridfinity/stl/bin-1x8x10h.stl
20.5 x 167.5 x 38.7
