karyandrew/hutchfinity/scad/gridfinity/stl/bin-4x4x20h.stl

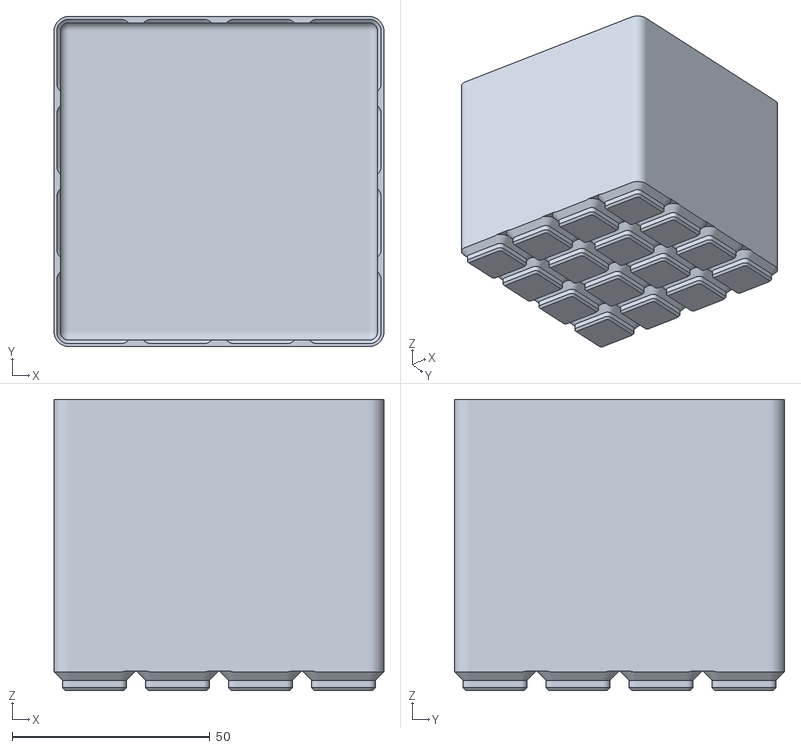
[picture p70: CAD file, 2026-06-07]
scad/gridfinity/stl/bin-4x4x20h.stl
83.5 x 83.5 x 73.7
