karyandrew/hutchfinity/scad/gridfinity/stl/bin-2x6x10h.stl

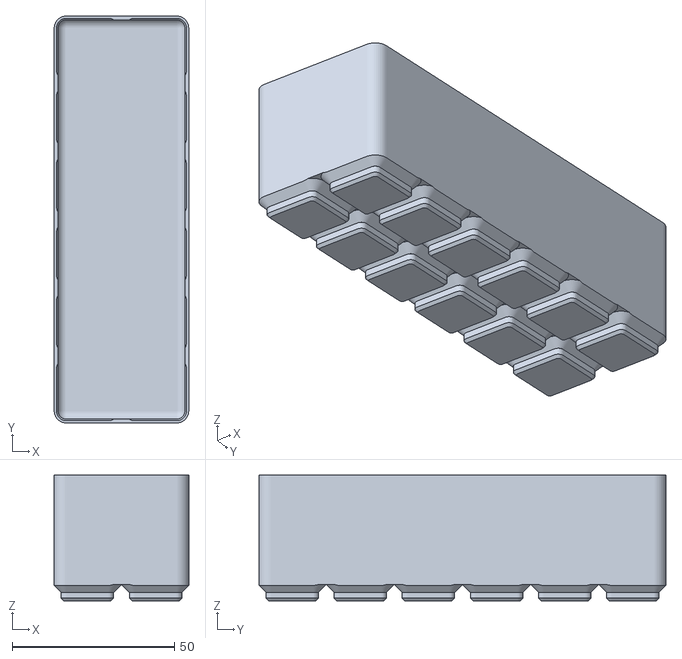
[picture p71: CAD file, 2026-06-07]
scad/gridfinity/stl/bin-2x6x10h.stl
41.5 x 125.5 x 38.7
