karyandrew/hutchfinity/scad/gridfinity/stl/baseplate-mega-cropped.stl

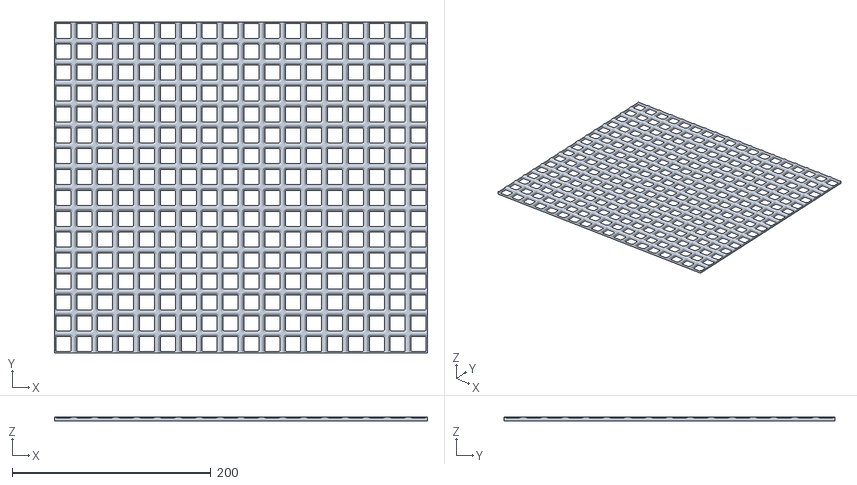
[picture p72: CAD file, 2026-06-07]
scad/gridfinity/stl/baseplate-mega-cropped.stl
375.0 x 333.0 x 4.00
