karyandrew/hutchfinity/scad/gridfinity/stl/bin-3x9x20h.stl

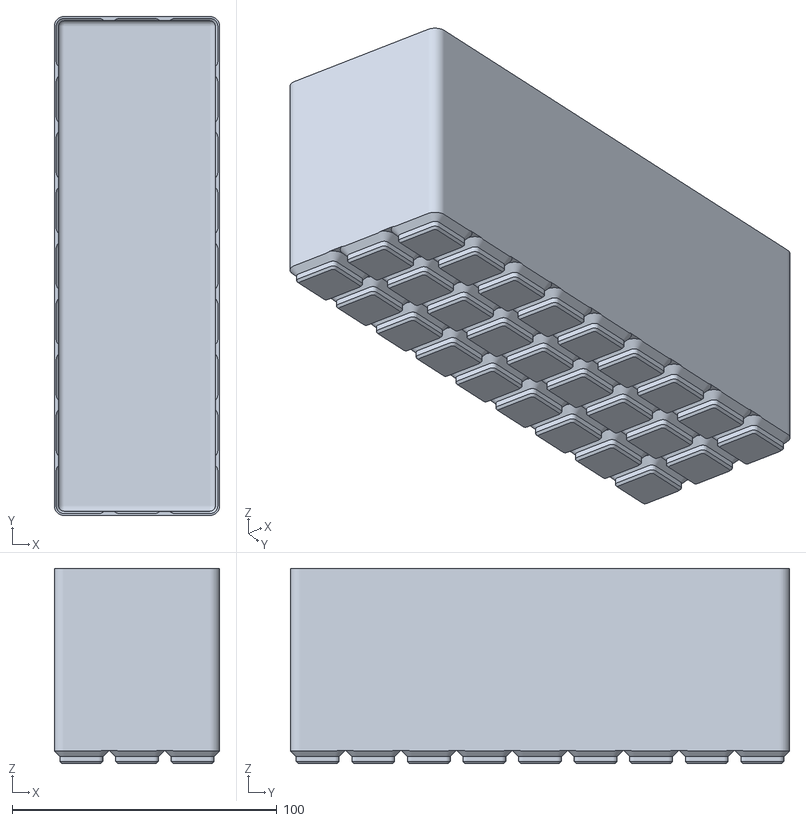
[picture p73: CAD file, 2026-06-07]
scad/gridfinity/stl/bin-3x9x20h.stl
62.5 x 188.5 x 73.7
