karyandrew/hutchfinity/scad/gridfinity/stl/bin-1x8x20h.stl

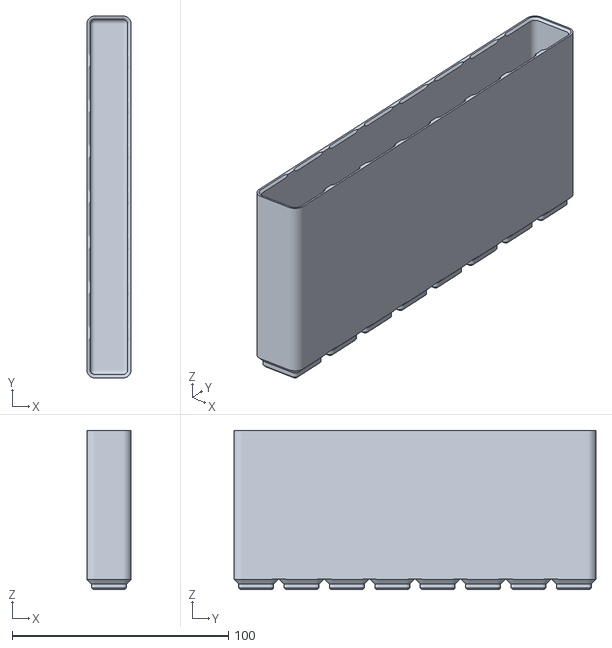
[picture p74: CAD file, 2026-06-07]
scad/gridfinity/stl/bin-1x8x20h.stl
20.5 x 167.5 x 73.7
