karyandrew/hutchfinity/scad/gridfinity/stl/bin-3x10x20h.stl

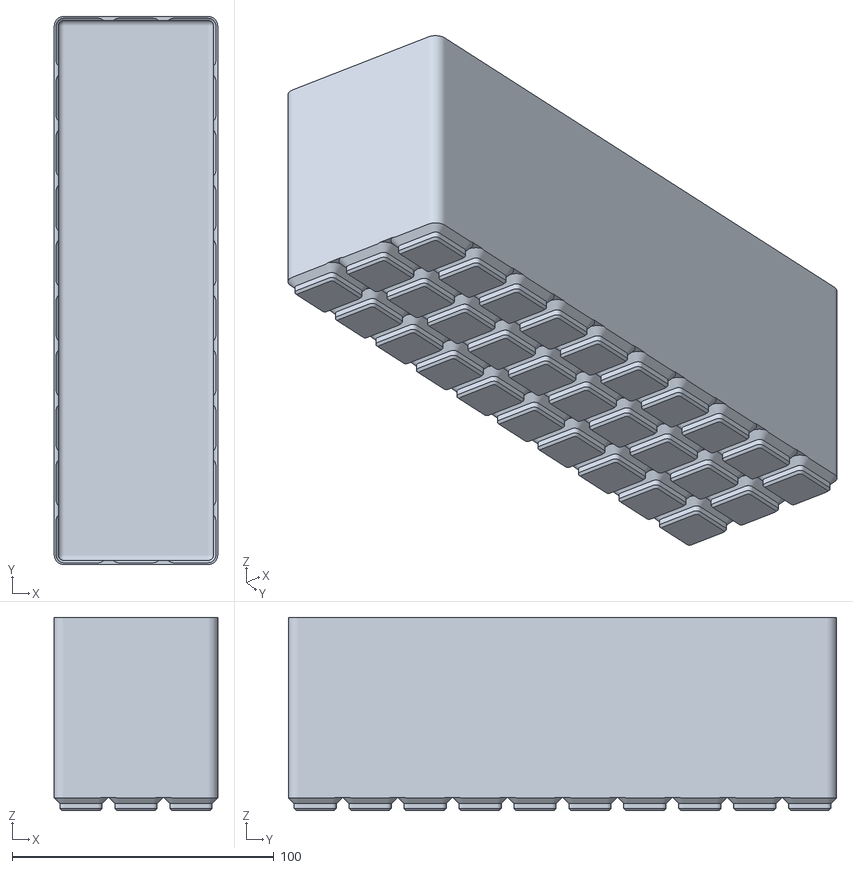
[picture p75: CAD file, 2026-06-07]
scad/gridfinity/stl/bin-3x10x20h.stl
62.5 x 209.5 x 73.7
