karyandrew/hutchfinity/scad/gridfinity/stl/bin-1x3x20h.stl

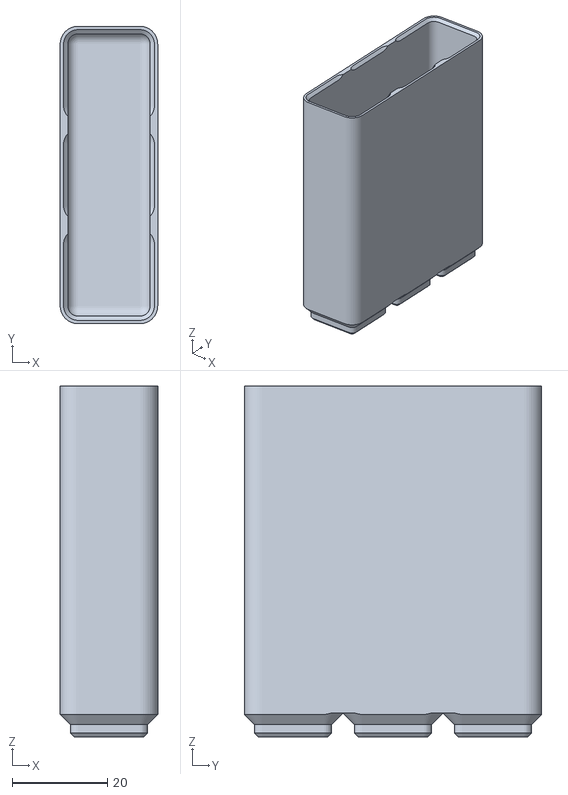
[picture p76: CAD file, 2026-06-07]
scad/gridfinity/stl/bin-1x3x20h.stl
20.5 x 62.5 x 73.7
