karyandrew/hutchfinity/scad/gridfinity/stl/bin-5x7x10h.stl

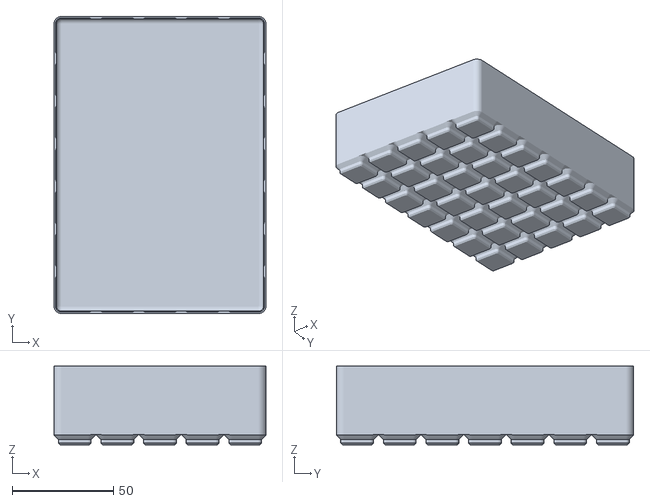
[picture p77: CAD file, 2026-06-07]
scad/gridfinity/stl/bin-5x7x10h.stl
104.5 x 146.5 x 38.7
