karyandrew/hutchfinity/scad/gridfinity/stl/bin-3x6x20h.stl

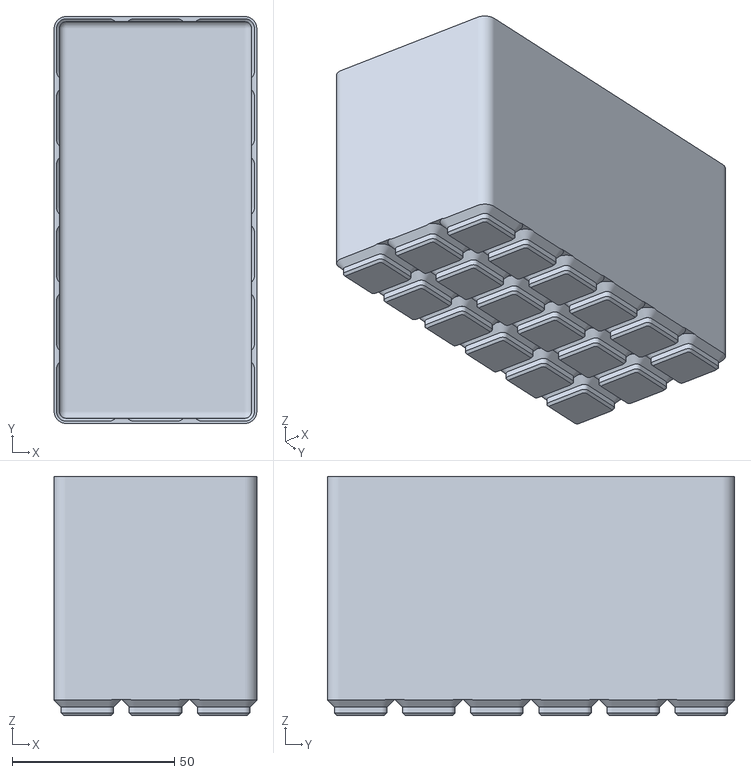
[picture p78: CAD file, 2026-06-07]
scad/gridfinity/stl/bin-3x6x20h.stl
62.5 x 125.5 x 73.7
