karyandrew/hutchfinity/scad/gridfinity/stl/bin-1x10x20h.stl

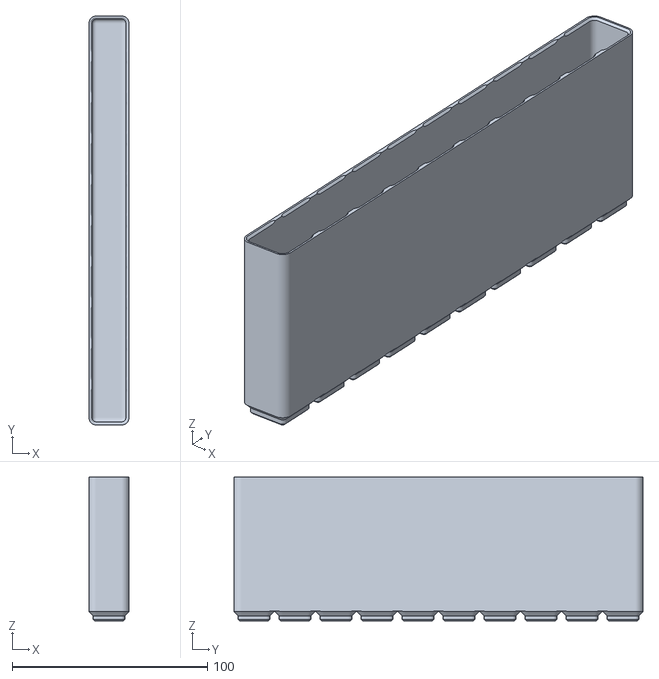
[picture p79: CAD file, 2026-06-07]
scad/gridfinity/stl/bin-1x10x20h.stl
20.5 x 209.5 x 73.7
