karyandrew/hutchfinity/scad/gridfinity/stl/bin-1x10x5h.stl

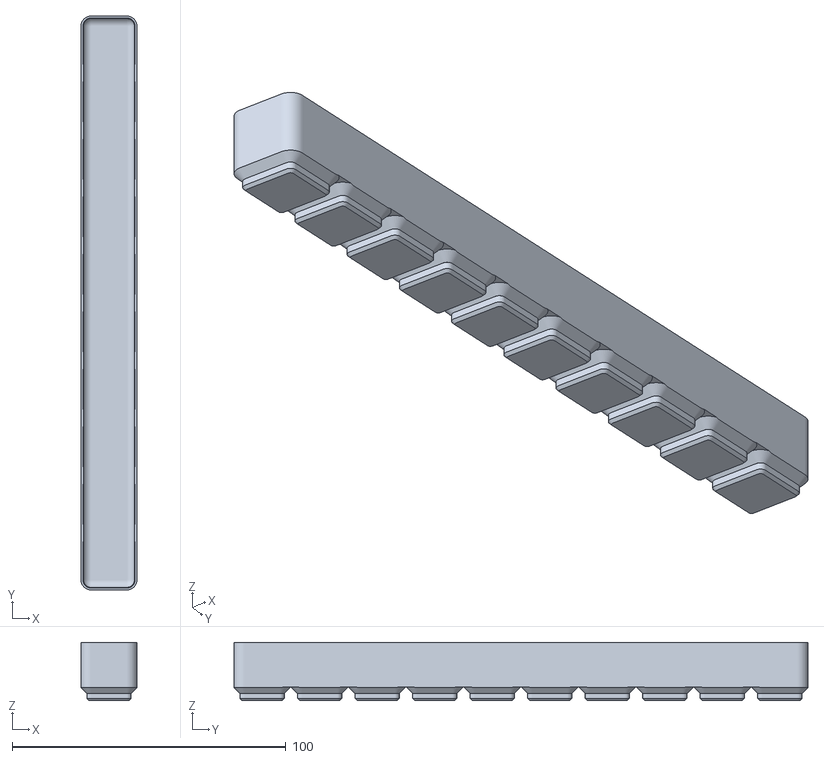
[picture p80: CAD file, 2026-06-07]
scad/gridfinity/stl/bin-1x10x5h.stl
20.5 x 209.5 x 21.2
