karyandrew/hutchfinity/scad/gridfinity/stl/bin-5x6x10h.stl

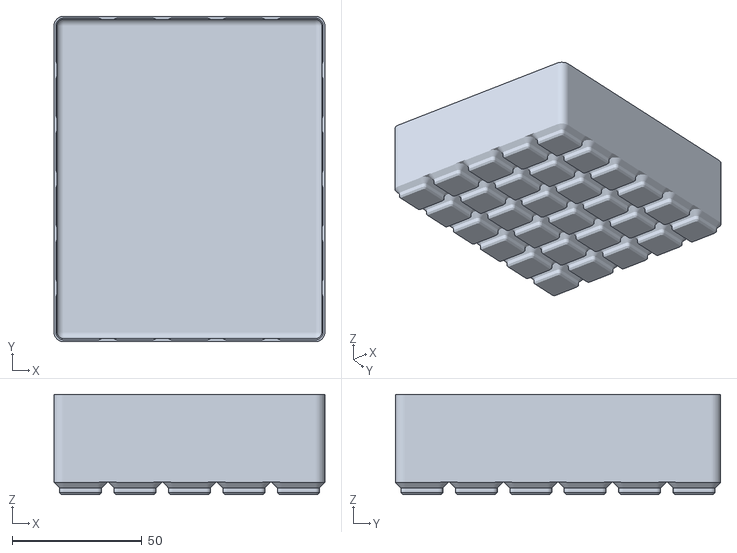
[picture p81: CAD file, 2026-06-07]
scad/gridfinity/stl/bin-5x6x10h.stl
104.5 x 125.5 x 38.7
