karyandrew/hutchfinity/scad/gridfinity/stl/bin-3x4x20h.stl

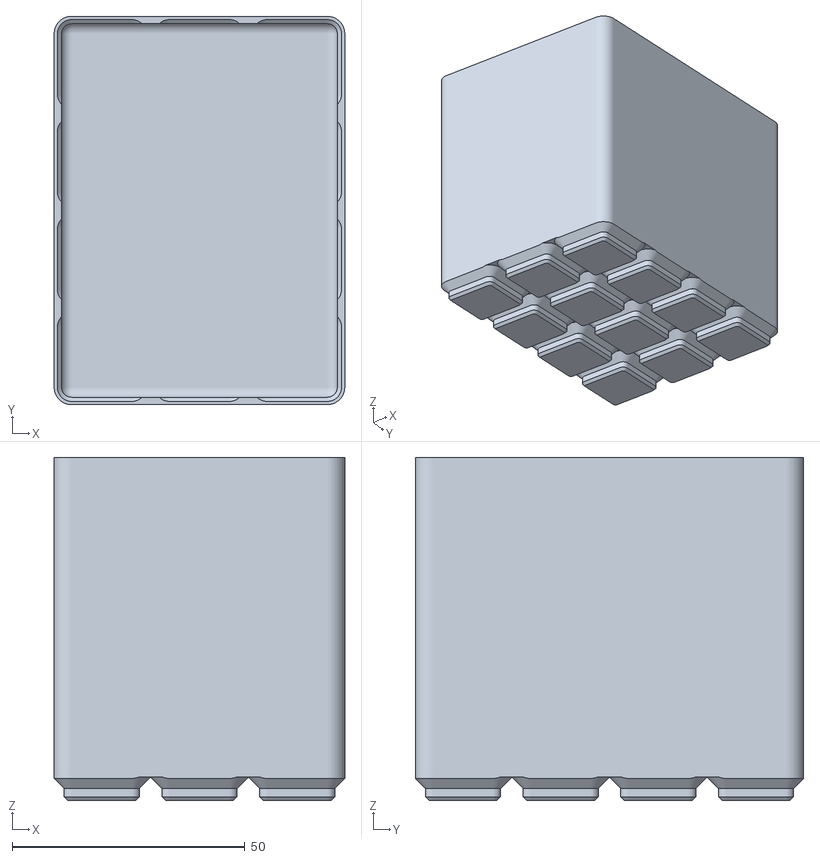
[picture p82: CAD file, 2026-06-07]
scad/gridfinity/stl/bin-3x4x20h.stl
62.5 x 83.5 x 73.7
