karyandrew/hutchfinity/scad/gridfinity/stl/bin-3x8x5h.stl

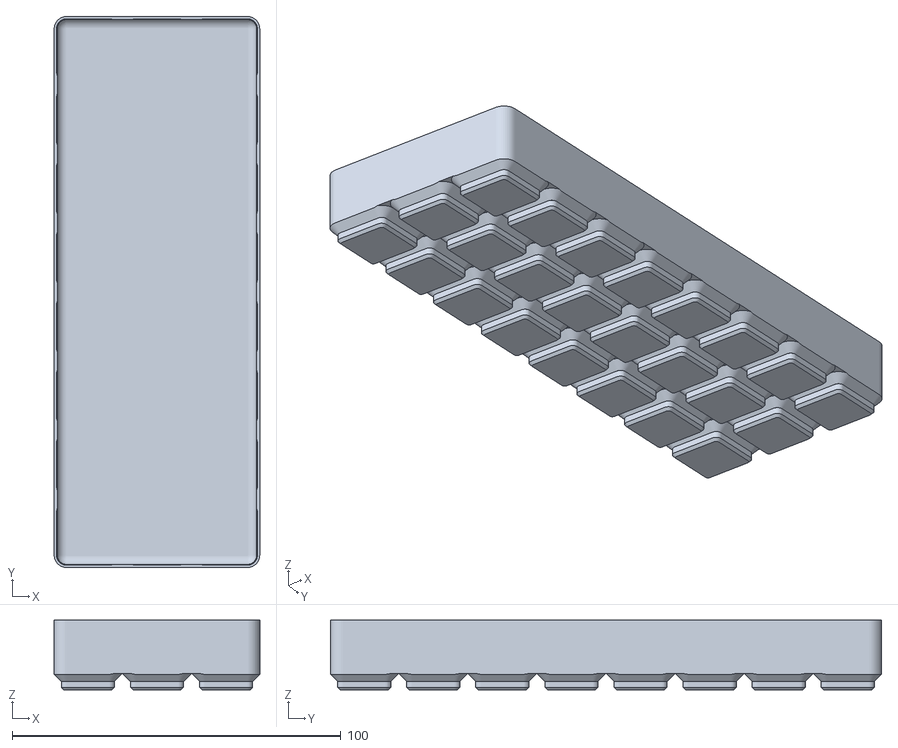
[picture p83: CAD file, 2026-06-07]
scad/gridfinity/stl/bin-3x8x5h.stl
62.5 x 167.5 x 21.2
