karyandrew/hutchfinity/scad/gridfinity/stl/bin-5x8x5h.stl

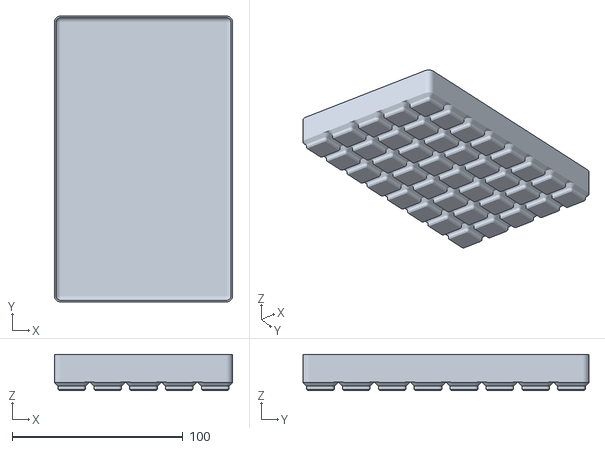
[picture p84: CAD file, 2026-06-07]
scad/gridfinity/stl/bin-5x8x5h.stl
104.5 x 167.5 x 21.2
