karyandrew/hutchfinity/scad/gridfinity/stl/bin-3x9x5h.stl

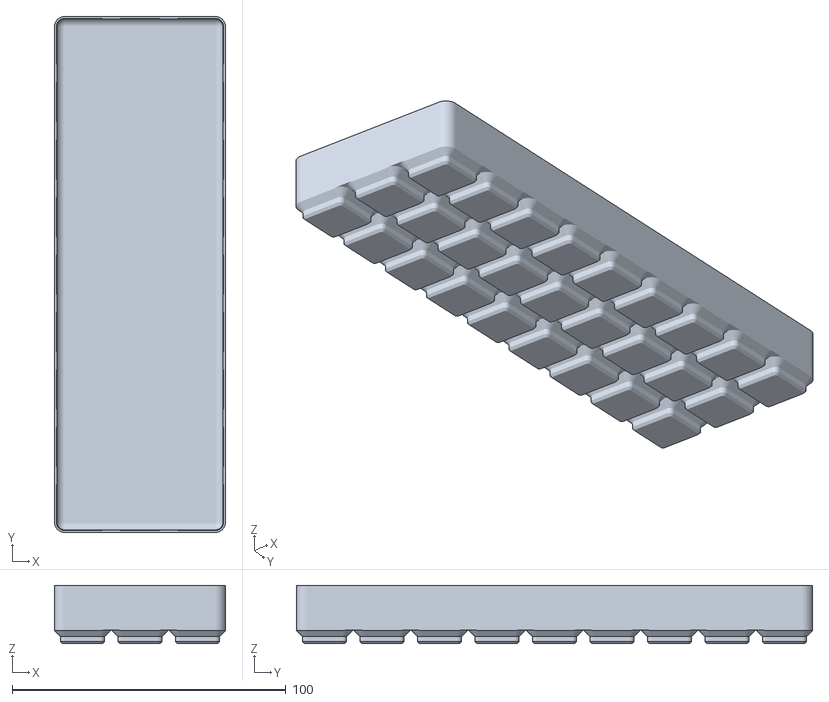
[picture p85: CAD file, 2026-06-07]
scad/gridfinity/stl/bin-3x9x5h.stl
62.5 x 188.5 x 21.2
