karyandrew/hutchfinity/scad/gridfinity/stl/bin-2x5x20h.stl

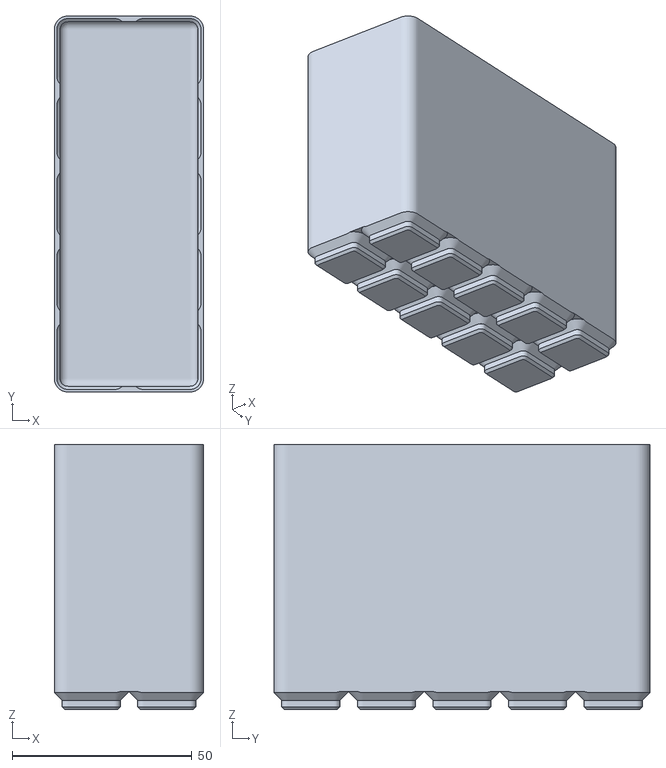
[picture p86: CAD file, 2026-06-07]
scad/gridfinity/stl/bin-2x5x20h.stl
41.5 x 104.5 x 73.7
