karyandrew/hutchfinity/scad/gridfinity/stl/bin-5x10x5h.stl

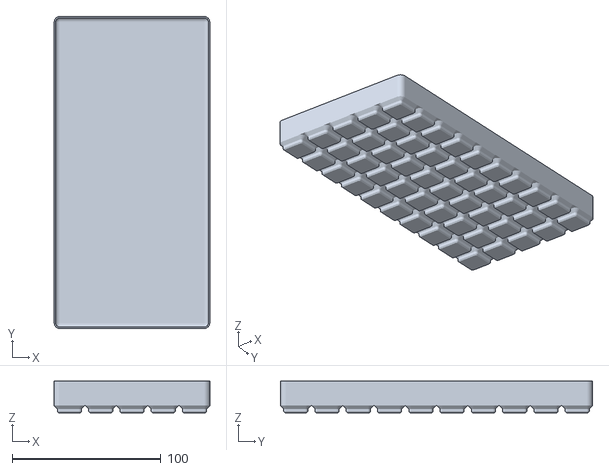
[picture p87: CAD file, 2026-06-07]
scad/gridfinity/stl/bin-5x10x5h.stl
104.5 x 209.5 x 21.2
