karyandrew/hutchfinity/scad/gridfinity/stl/bin-4x10x20h.stl

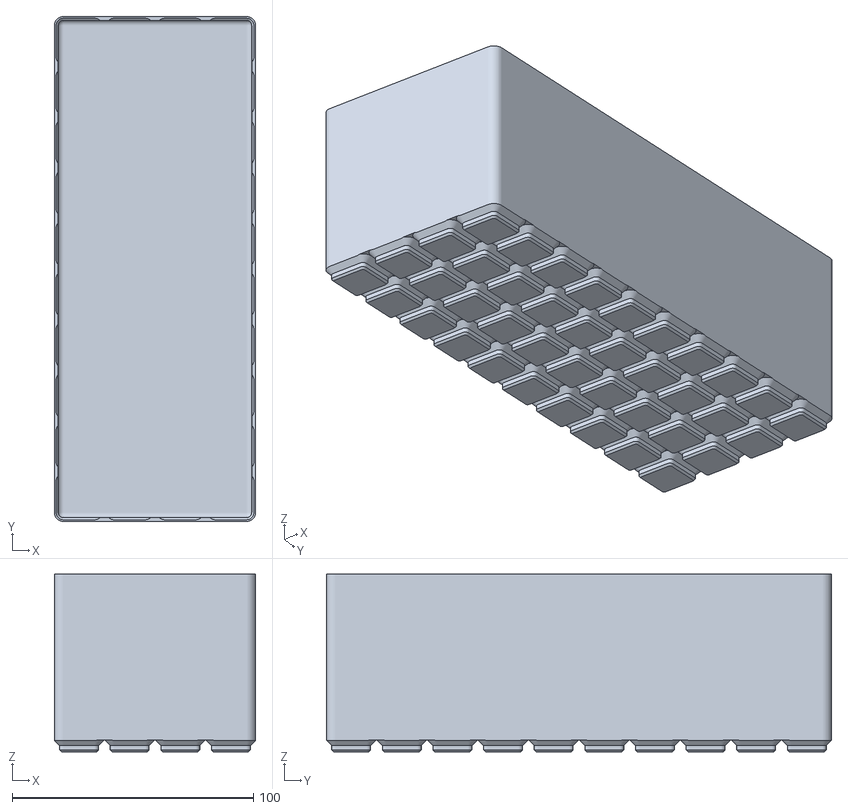
[picture p88: CAD file, 2026-06-07]
scad/gridfinity/stl/bin-4x10x20h.stl
83.5 x 209.5 x 73.7
