karyandrew/hutchfinity/scad/gridfinity/stl/bin-3x9x10h.stl

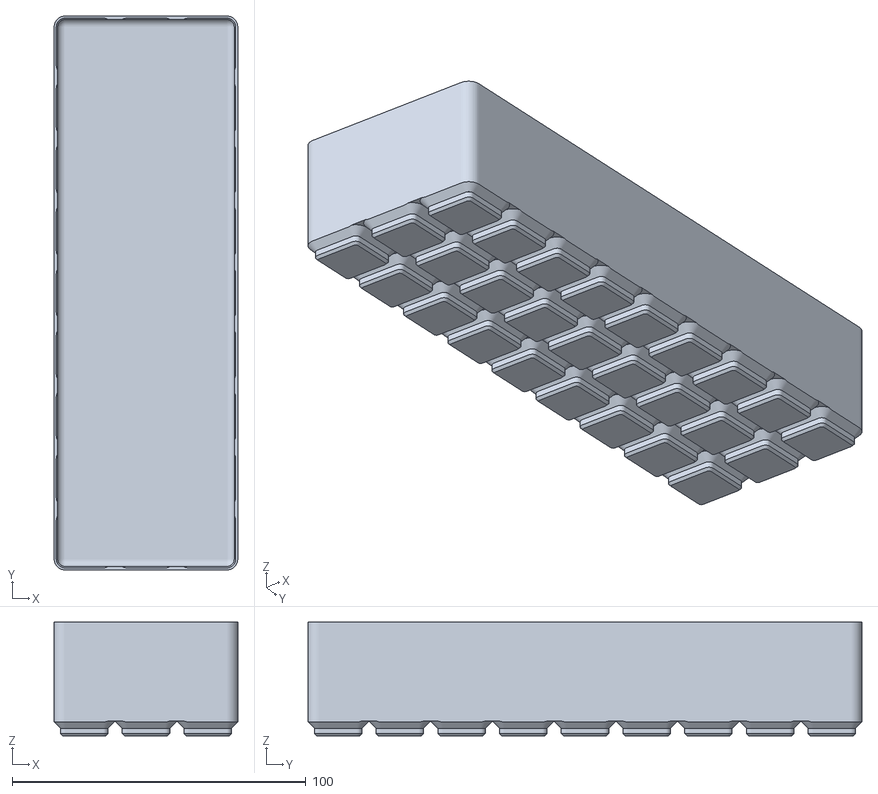
[picture p89: CAD file, 2026-06-07]
scad/gridfinity/stl/bin-3x9x10h.stl
62.5 x 188.5 x 38.7
