karyandrew/hutchfinity/scad/gridfinity/stl/bin-1x5x20h.stl

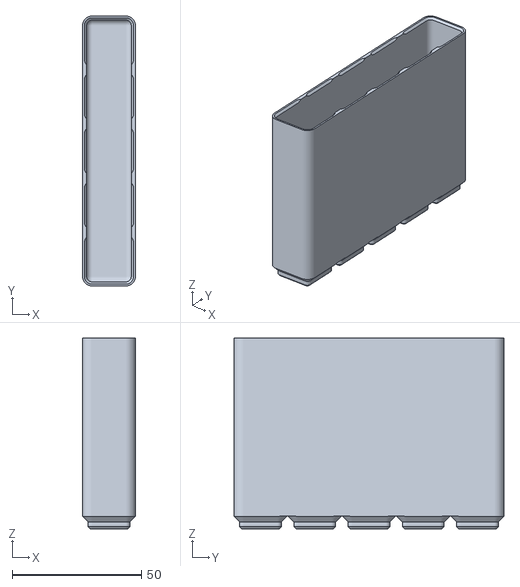
[picture p90: CAD file, 2026-06-07]
scad/gridfinity/stl/bin-1x5x20h.stl
20.5 x 104.5 x 73.7
