karyandrew/hutchfinity/scad/gridfinity/stl/bin-2x7x10h.stl

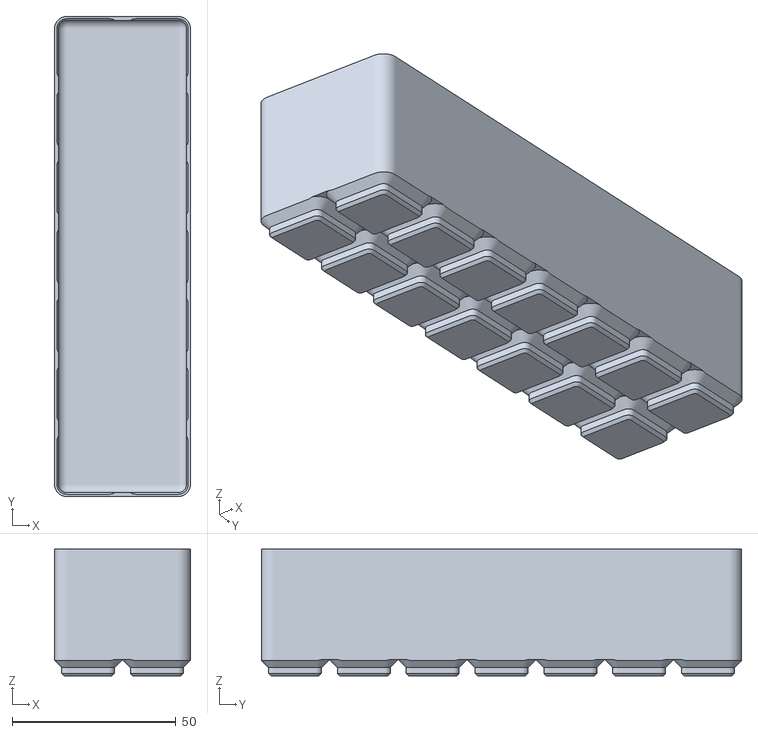
[picture p91: CAD file, 2026-06-07]
scad/gridfinity/stl/bin-2x7x10h.stl
41.5 x 146.5 x 38.7
