karyandrew/hutchfinity/scad/gridfinity/stl/bin-4x5x5h.stl

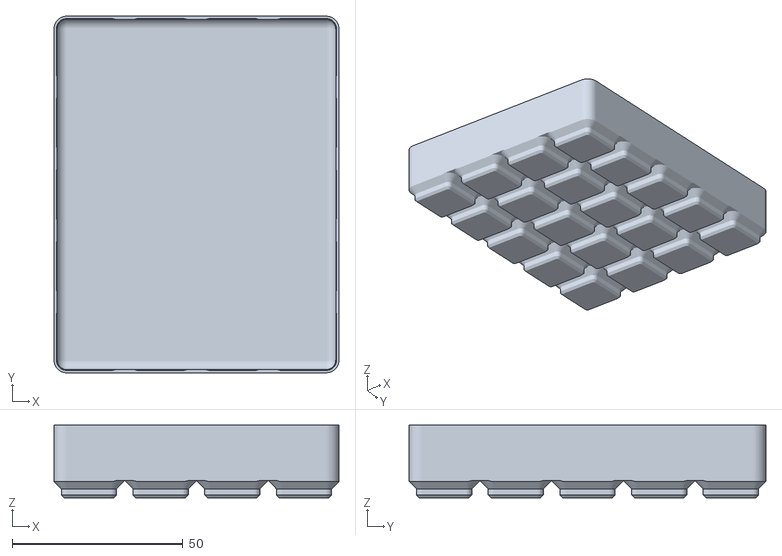
[picture p92: CAD file, 2026-06-07]
scad/gridfinity/stl/bin-4x5x5h.stl
83.5 x 104.5 x 21.2
