karyandrew/hutchfinity/scad/gridfinity/stl/bin-1x2x20h.stl

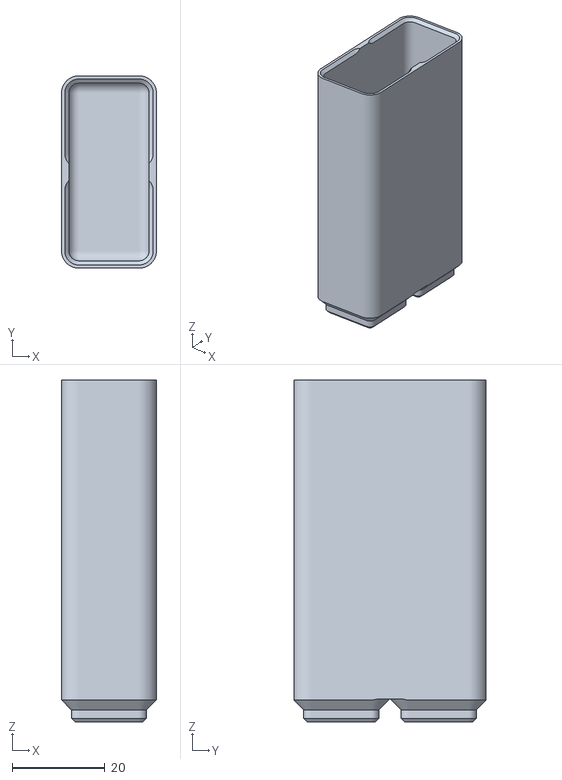
[picture p93: CAD file, 2026-06-07]
scad/gridfinity/stl/bin-1x2x20h.stl
20.5 x 41.5 x 73.7
