karyandrew/hutchfinity/scad/gridfinity/stl/bin-1x6x5h.stl

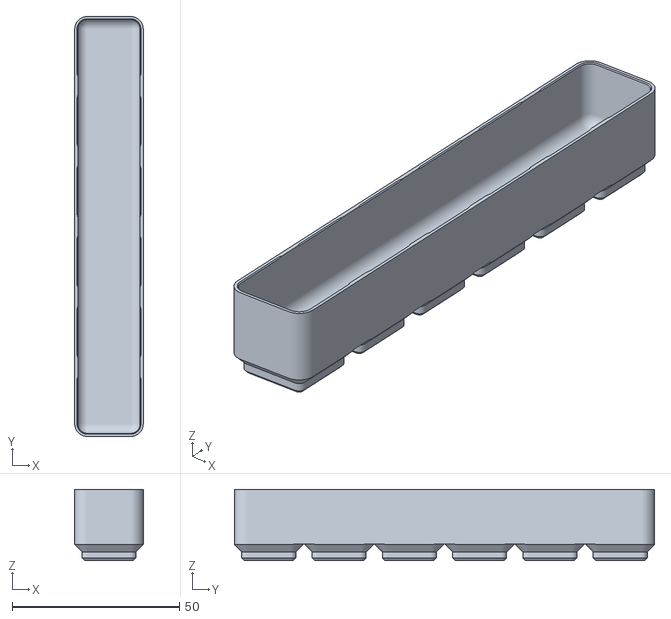
[picture p94: CAD file, 2026-06-07]
scad/gridfinity/stl/bin-1x6x5h.stl
20.5 x 125.5 x 21.2
