karyandrew/hutchfinity/scad/gridfinity/stl/bin-3x7x5h.stl

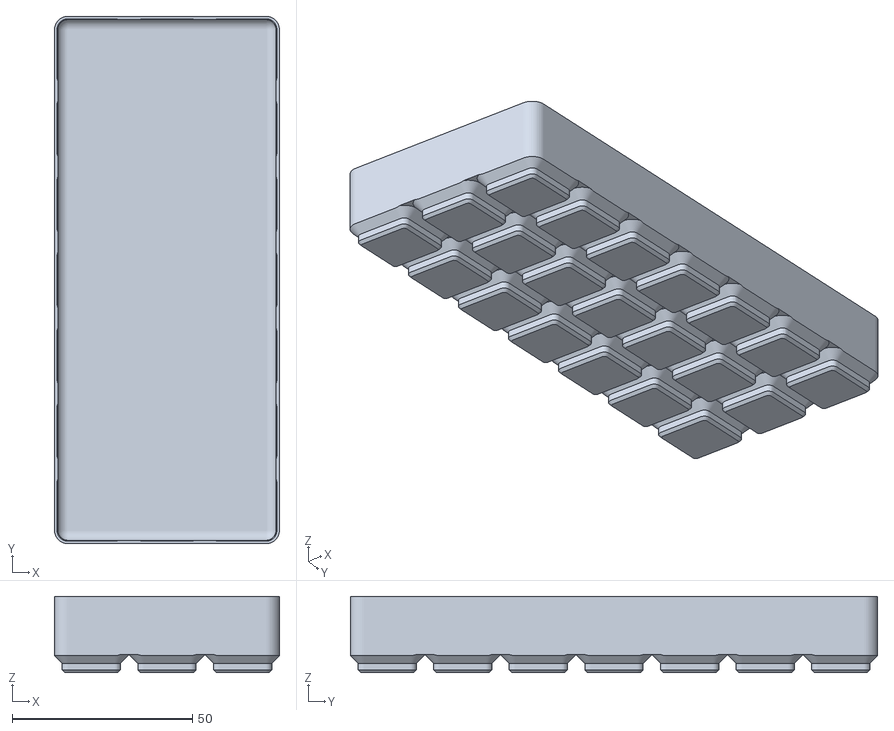
[picture p95: CAD file, 2026-06-07]
scad/gridfinity/stl/bin-3x7x5h.stl
62.5 x 146.5 x 21.2
