karyandrew/hutchfinity/scad/gridfinity/stl/bin-4x4x10h.stl

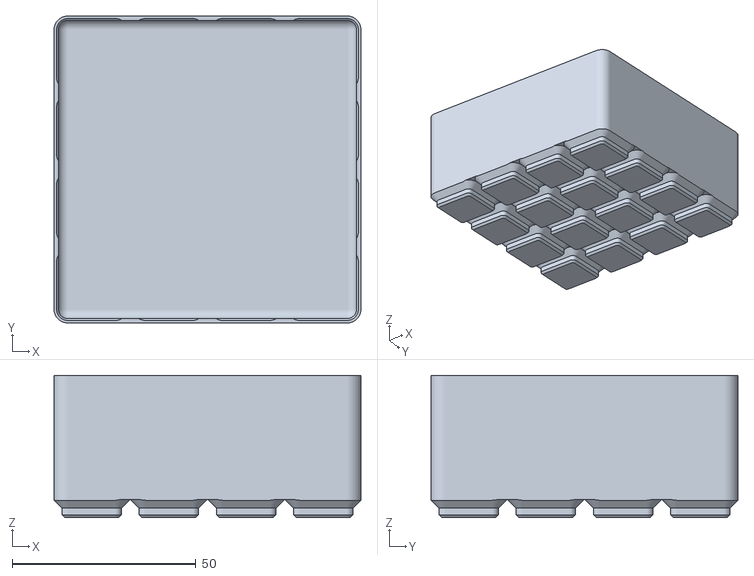
[picture p96: CAD file, 2026-06-07]
scad/gridfinity/stl/bin-4x4x10h.stl
83.5 x 83.5 x 38.7
