karyandrew/hutchfinity/scad/gridfinity/stl/bin-2x3x20h.stl

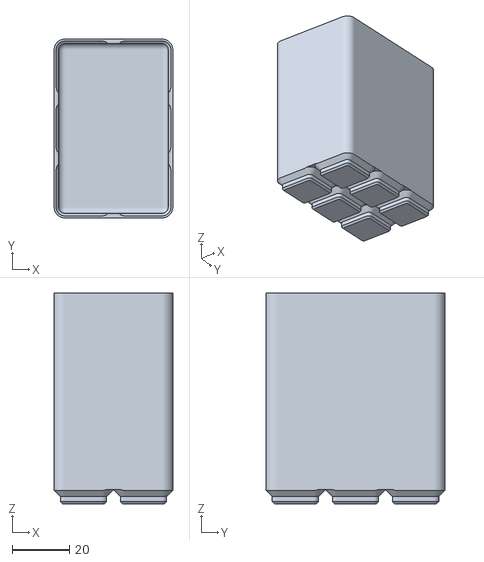
[picture p97: CAD file, 2026-06-07]
scad/gridfinity/stl/bin-2x3x20h.stl
41.5 x 62.5 x 73.7
