karyandrew/hutchfinity/scad/gridfinity/stl/bin-1x3x5h.stl

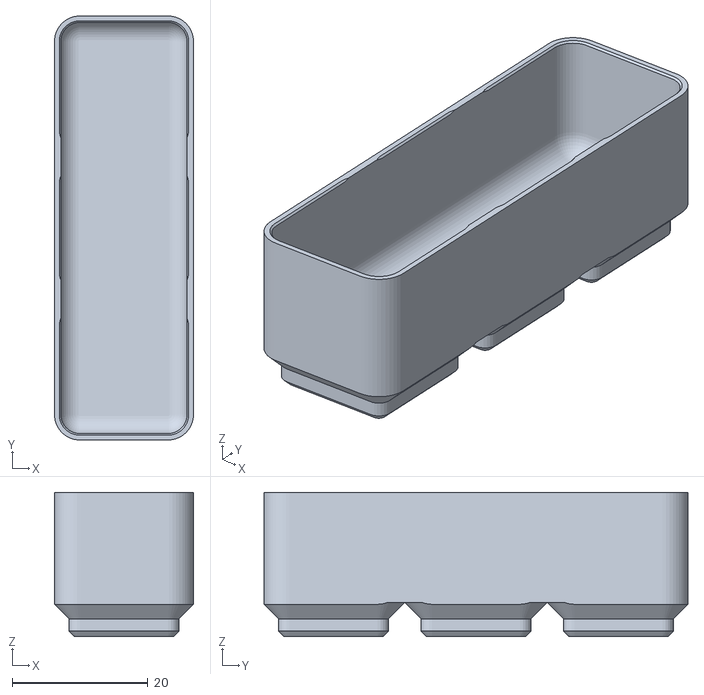
[picture p98: CAD file, 2026-06-07]
scad/gridfinity/stl/bin-1x3x5h.stl
20.5 x 62.5 x 21.2
