karyandrew/hutchfinity/scad/gridfinity/stl/bin-1x4x10h.stl

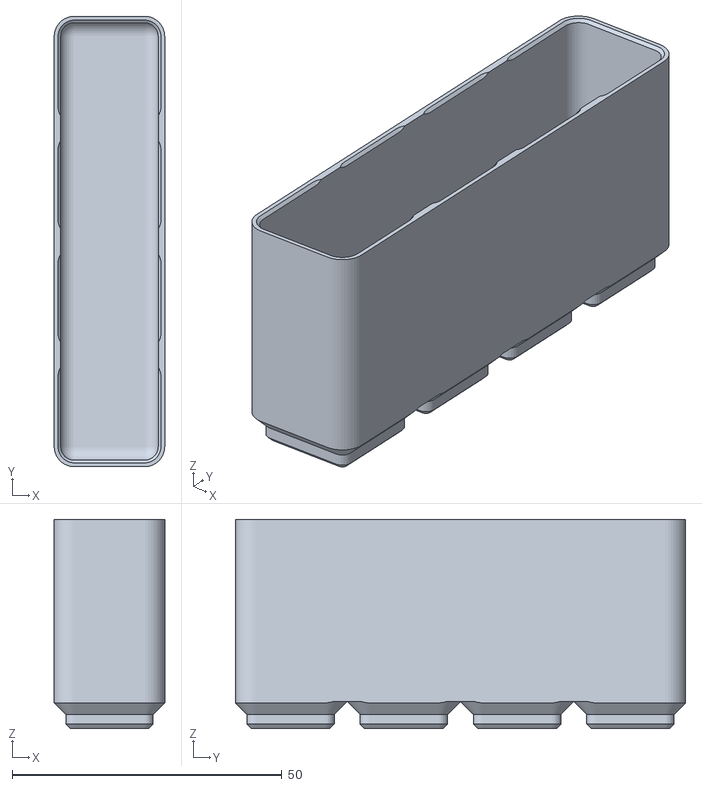
[picture p99: CAD file, 2026-06-07]
scad/gridfinity/stl/bin-1x4x10h.stl
20.5 x 83.5 x 38.7
