karyandrew/hutchfinity/scad/gridfinity/stl/bin-5x6x20h.stl

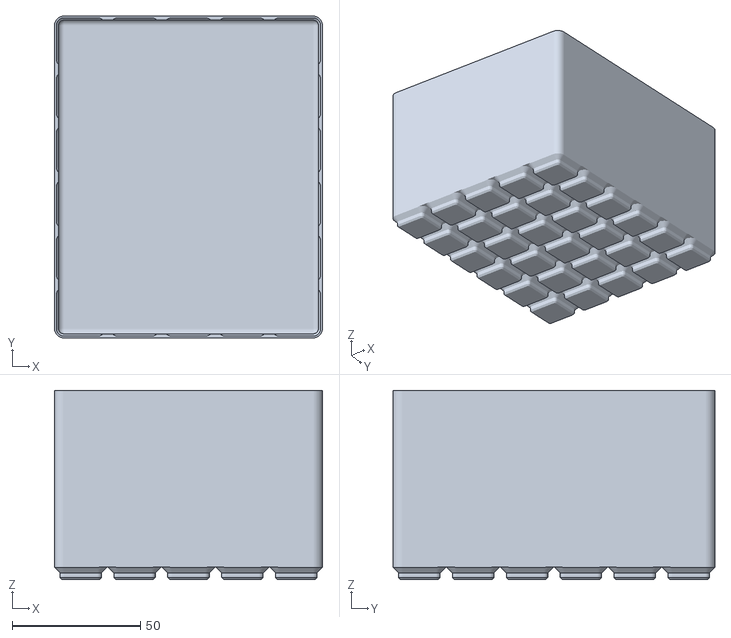
[picture p100: CAD file, 2026-06-07]
scad/gridfinity/stl/bin-5x6x20h.stl
104.5 x 125.5 x 73.7
