karyandrew/hutchfinity/scad/gridfinity/stl/bin-1x5x10h.stl

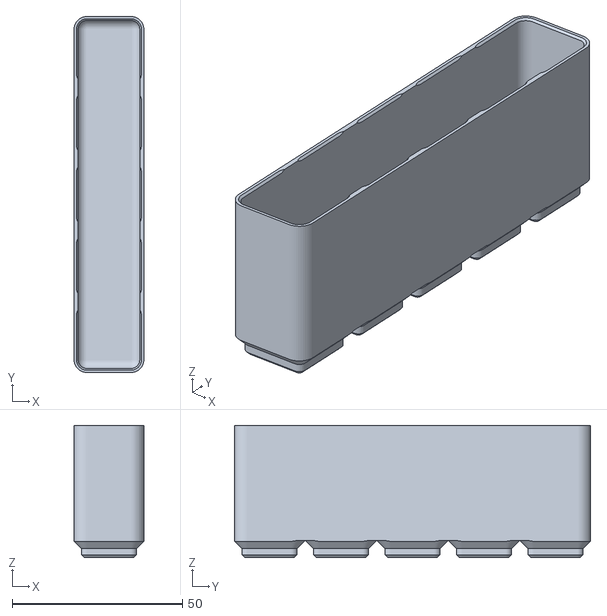
[picture p101: CAD file, 2026-06-07]
scad/gridfinity/stl/bin-1x5x10h.stl
20.5 x 104.5 x 38.7
