karyandrew/hutchfinity/scad/gridfinity/stl/bin-2x7x20h.stl

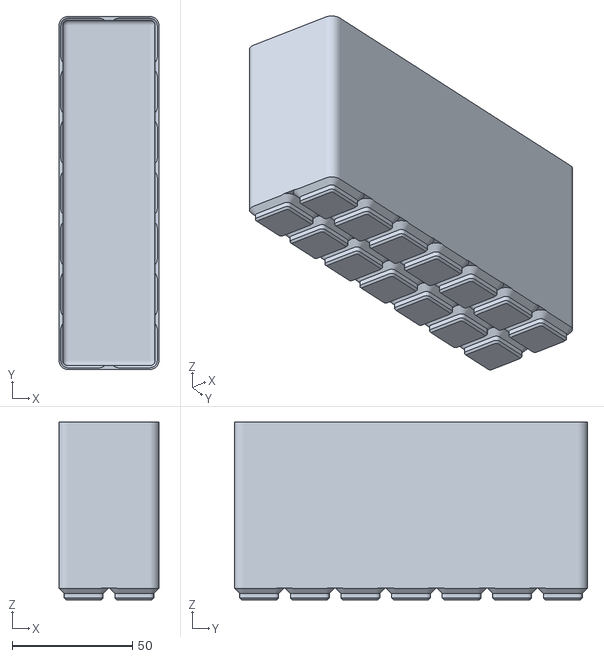
[picture p102: CAD file, 2026-06-07]
scad/gridfinity/stl/bin-2x7x20h.stl
41.5 x 146.5 x 73.7
