karyandrew/hutchfinity/scad/gridfinity/stl/bin-5x9x20h.stl

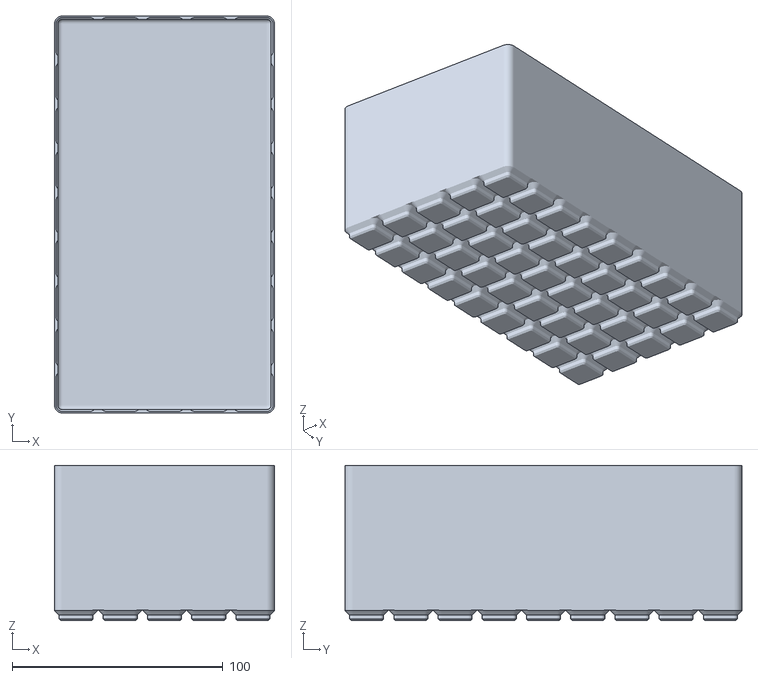
[picture p103: CAD file, 2026-06-07]
scad/gridfinity/stl/bin-5x9x20h.stl
104.5 x 188.5 x 73.7
