karyandrew/hutchfinity/scad/gridfinity/stl/bin-1x5x5h.stl

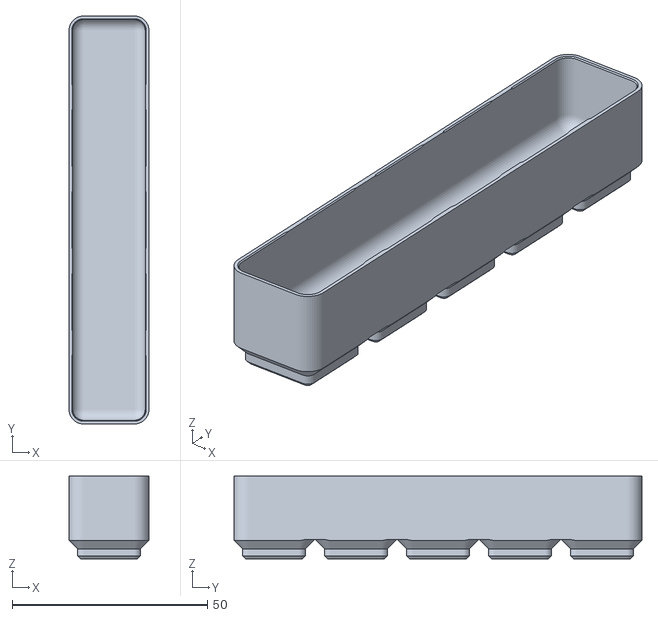
[picture p104: CAD file, 2026-06-07]
scad/gridfinity/stl/bin-1x5x5h.stl
20.5 x 104.5 x 21.2
