karyandrew/hutchfinity/scad/gridfinity/stl/bin-5x9x10h.stl

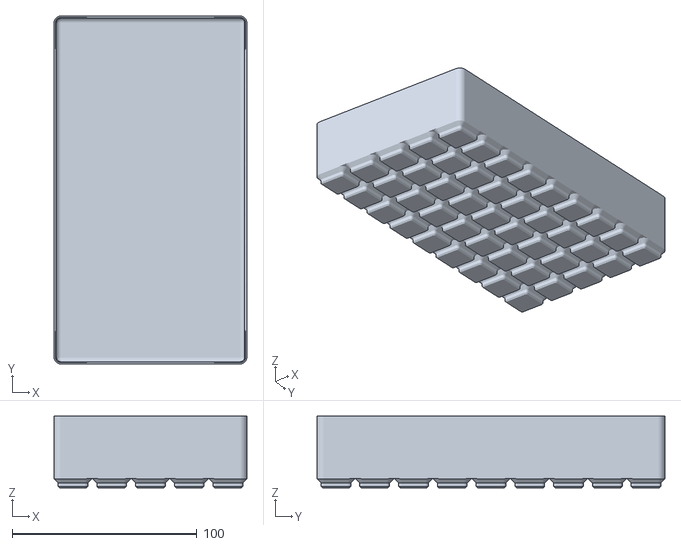
[picture p105: CAD file, 2026-06-07]
scad/gridfinity/stl/bin-5x9x10h.stl
104.5 x 188.5 x 38.7
