karyandrew/hutchfinity/scad/gridfinity/stl/bin-4x5x10h.stl

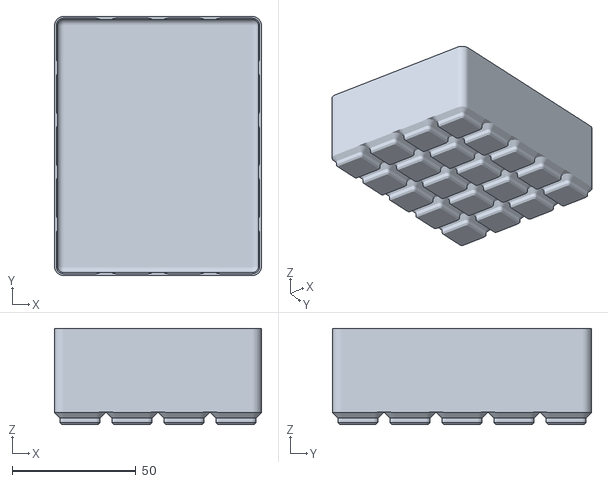
[picture p106: CAD file, 2026-06-07]
scad/gridfinity/stl/bin-4x5x10h.stl
83.5 x 104.5 x 38.7
