karyandrew/hutchfinity/scad/gridfinity/stl/bin-2x5x5h.stl

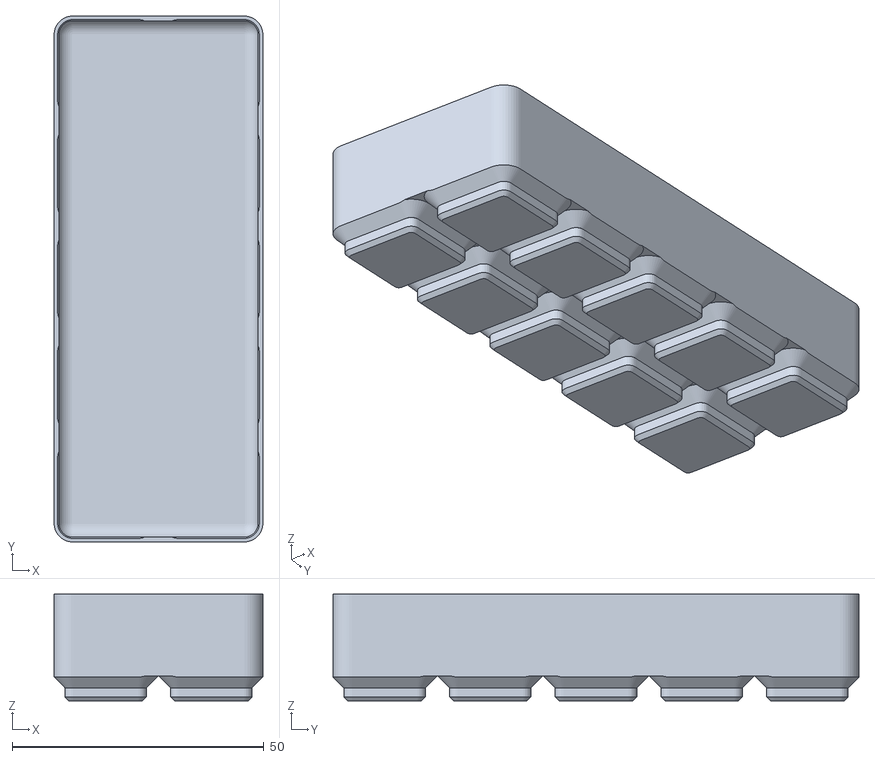
[picture p107: CAD file, 2026-06-07]
scad/gridfinity/stl/bin-2x5x5h.stl
41.5 x 104.5 x 21.2
