karyandrew/hutchfinity/scad/gridfinity/stl/tub-mini-20u.stl

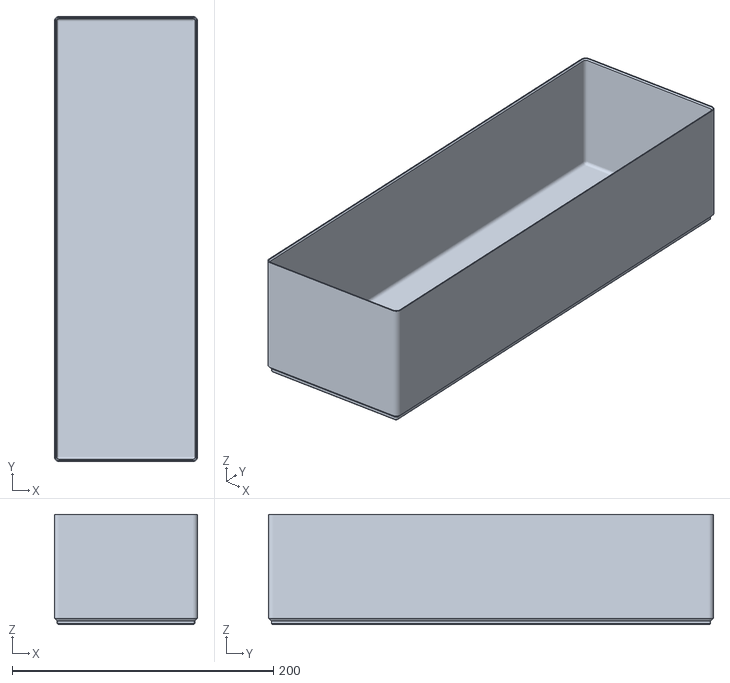
[picture p108: CAD file, 2026-06-07]
scad/gridfinity/stl/tub-mini-20u.stl
109.7 x 340.7 x 84.2
