karyandrew/hutchfinity/scad/gridfinity/stl/bin-4x5x20h.stl

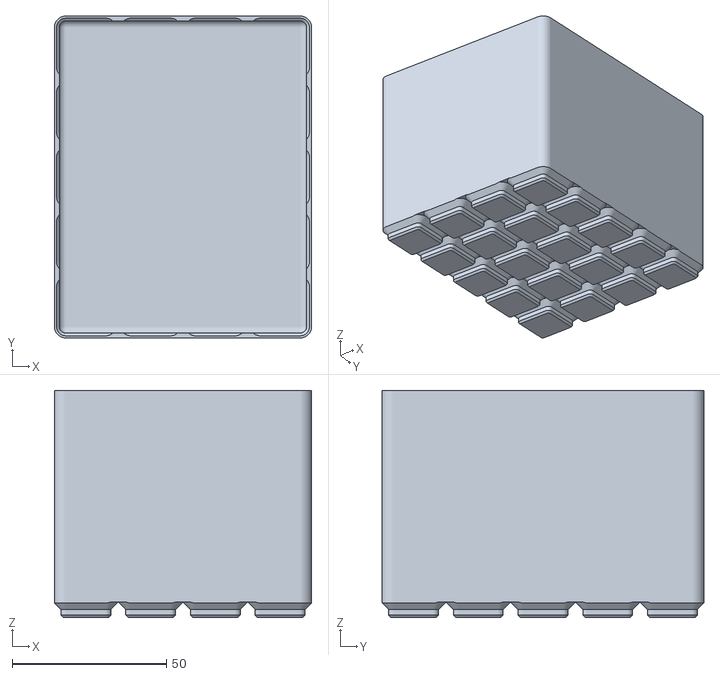
[picture p109: CAD file, 2026-06-07]
scad/gridfinity/stl/bin-4x5x20h.stl
83.5 x 104.5 x 73.7
