karyandrew/hutchfinity/scad/gridfinity/stl/bin-3x8x10h.stl

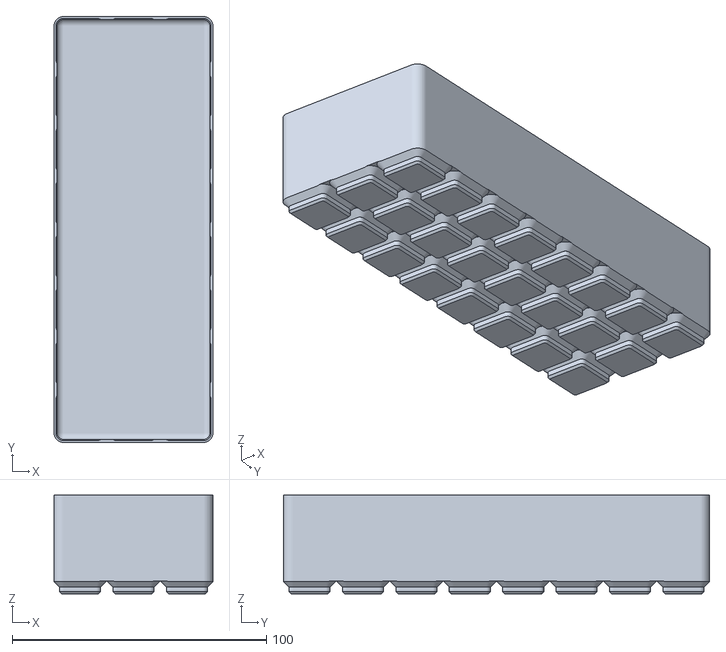
[picture p110: CAD file, 2026-06-07]
scad/gridfinity/stl/bin-3x8x10h.stl
62.5 x 167.5 x 38.7
