karyandrew/hutchfinity/scad/gridfinity/stl/bin-4x6x5h.stl

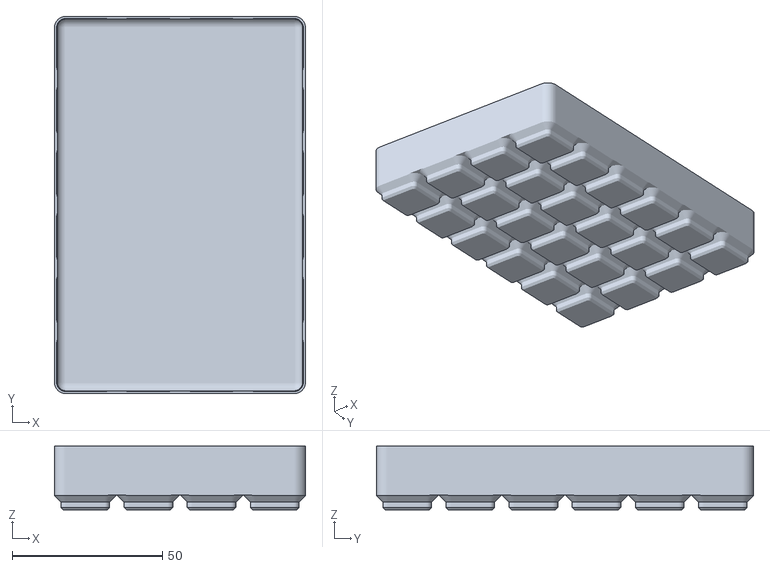
[picture p111: CAD file, 2026-06-07]
scad/gridfinity/stl/bin-4x6x5h.stl
83.5 x 125.5 x 21.2
