karyandrew/hutchfinity/scad/gridfinity/stl/bin-4x7x20h.stl

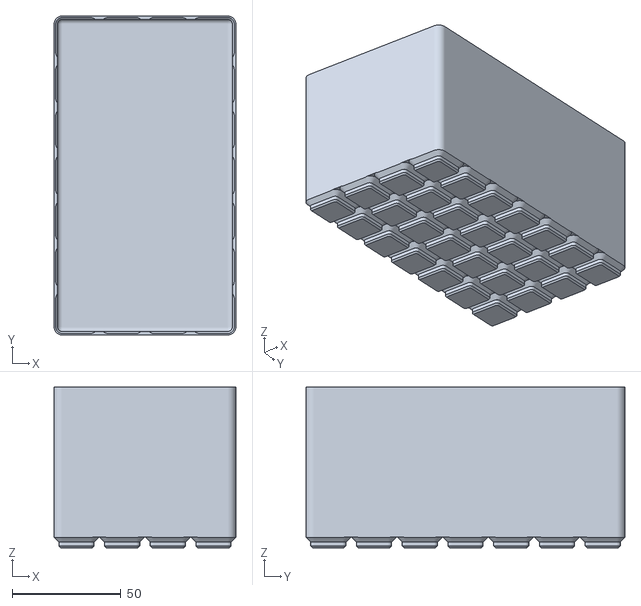
[picture p112: CAD file, 2026-06-07]
scad/gridfinity/stl/bin-4x7x20h.stl
83.5 x 146.5 x 73.7
