karyandrew/hutchfinity/scad/gridfinity/stl/bin-2x4x20h.stl

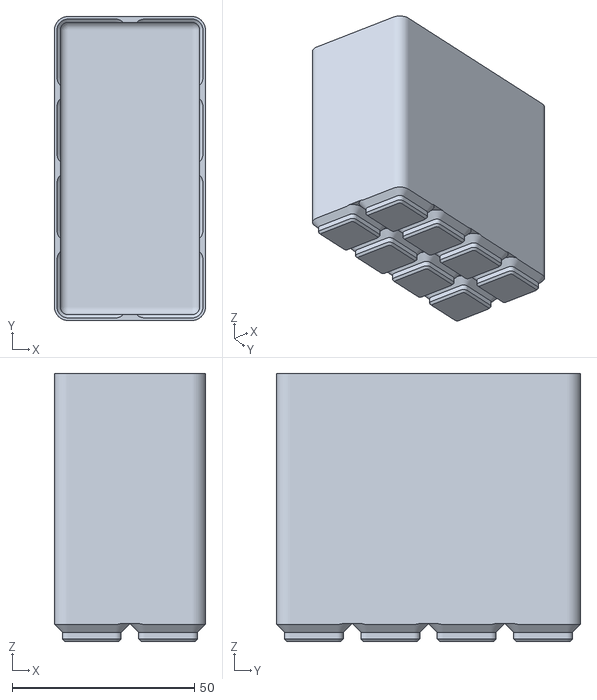
[picture p113: CAD file, 2026-06-07]
scad/gridfinity/stl/bin-2x4x20h.stl
41.5 x 83.5 x 73.7
