karyandrew/hutchfinity/scad/gridfinity/stl/bin-1x3x10h.stl

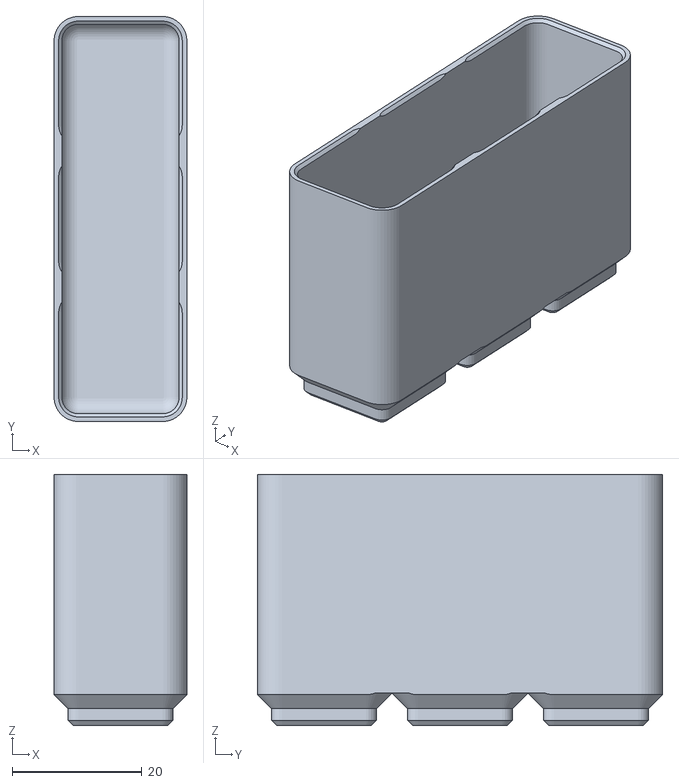
[picture p114: CAD file, 2026-06-07]
scad/gridfinity/stl/bin-1x3x10h.stl
20.5 x 62.5 x 38.7
