karyandrew/hutchfinity/scad/gridfinity/stl/bin-5x5x20h.stl

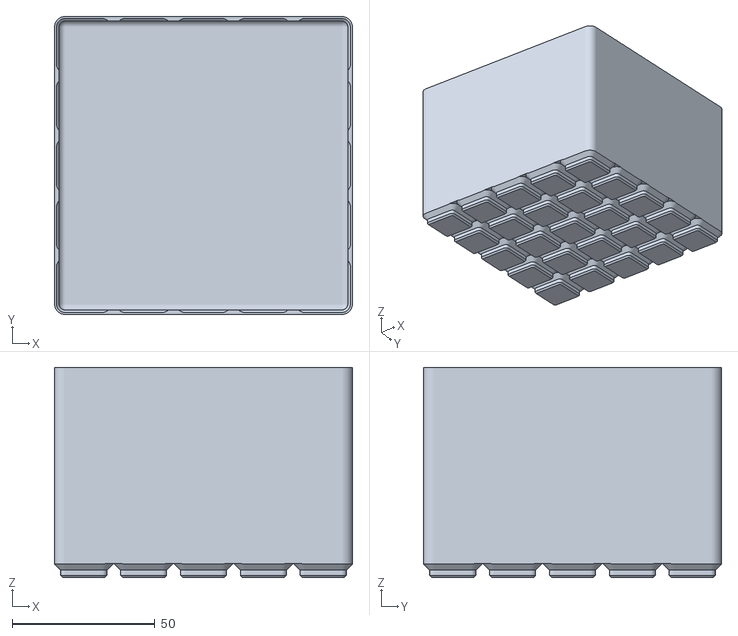
[picture p115: CAD file, 2026-06-07]
scad/gridfinity/stl/bin-5x5x20h.stl
104.5 x 104.5 x 73.7
