karyandrew/hutchfinity/scad/gridfinity/stl/bin-3x3x10h.stl

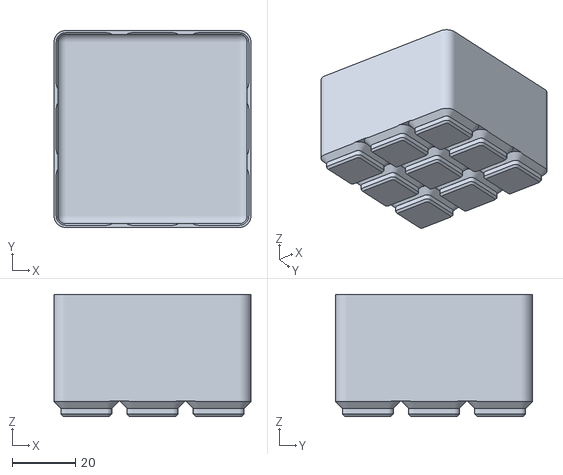
[picture p116: CAD file, 2026-06-07]
scad/gridfinity/stl/bin-3x3x10h.stl
62.5 x 62.5 x 38.7
