karyandrew/hutchfinity/scad/gridfinity/stl/bin-2x5x10h.stl

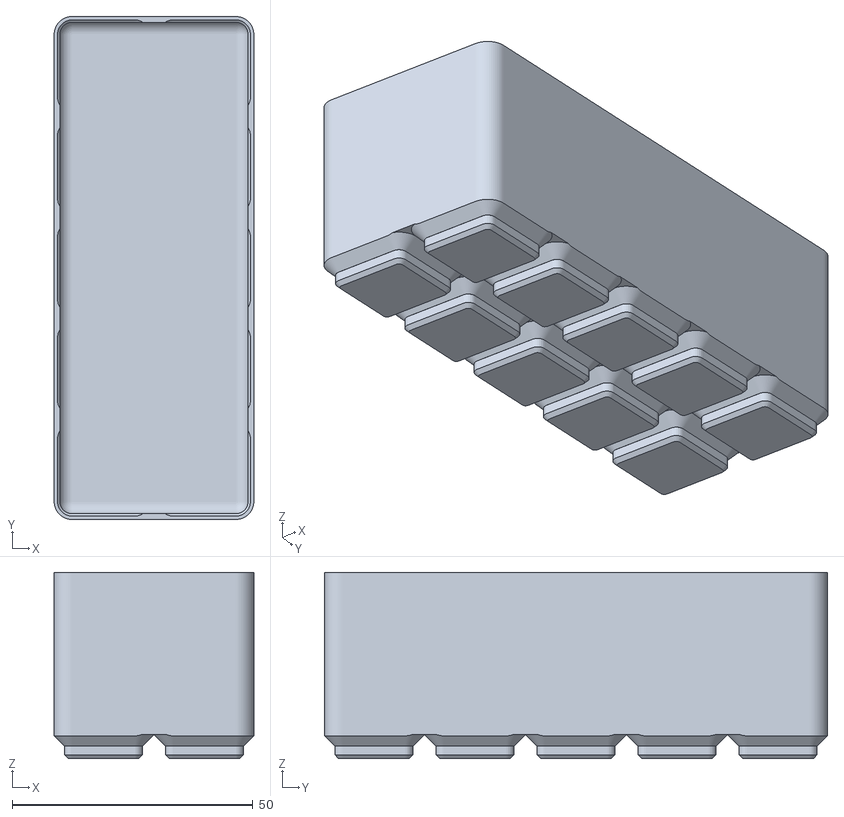
[picture p117: CAD file, 2026-06-07]
scad/gridfinity/stl/bin-2x5x10h.stl
41.5 x 104.5 x 38.7
