karyandrew/hutchfinity/scad/gridfinity/stl/bin-4x6x10h.stl

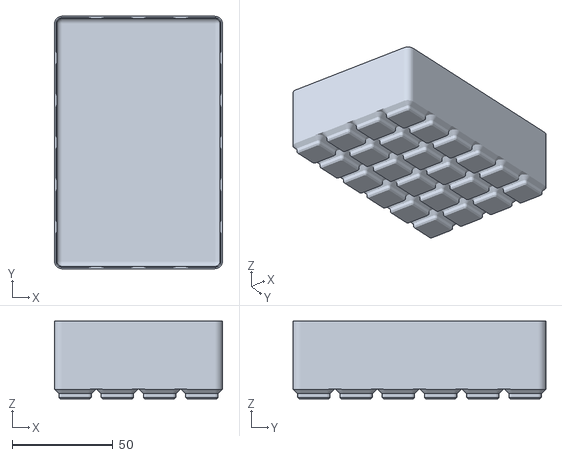
[picture p118: CAD file, 2026-06-07]
scad/gridfinity/stl/bin-4x6x10h.stl
83.5 x 125.5 x 38.7
