karyandrew/hutchfinity/scad/gridfinity/stl/bin-2x2x5h.stl

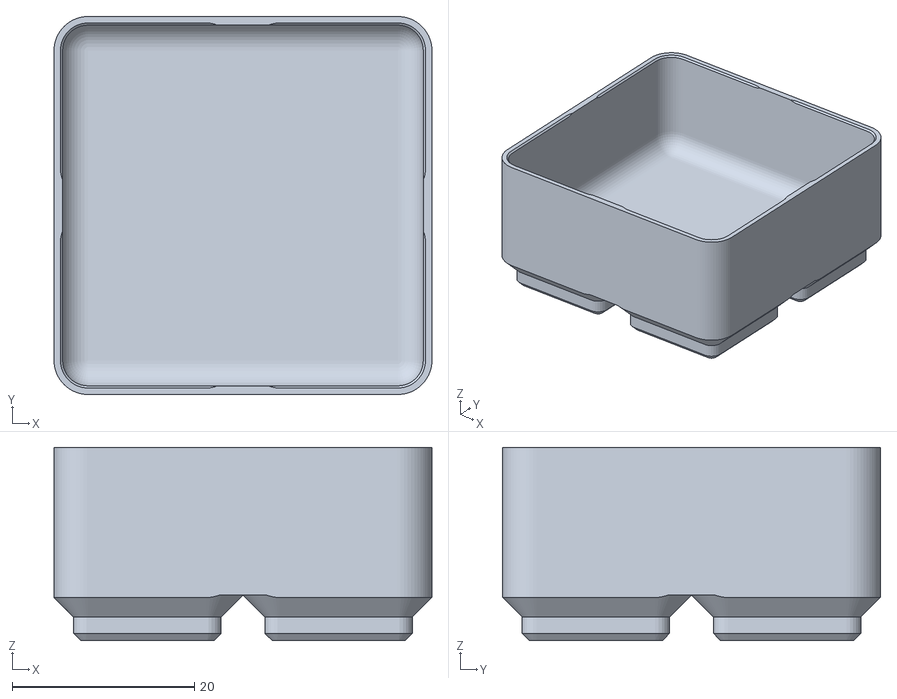
[picture p119: CAD file, 2026-06-07]
scad/gridfinity/stl/bin-2x2x5h.stl
41.5 x 41.5 x 21.2
