karyandrew/hutchfinity/scad/gridfinity/stl/bin-3x5x10h.stl

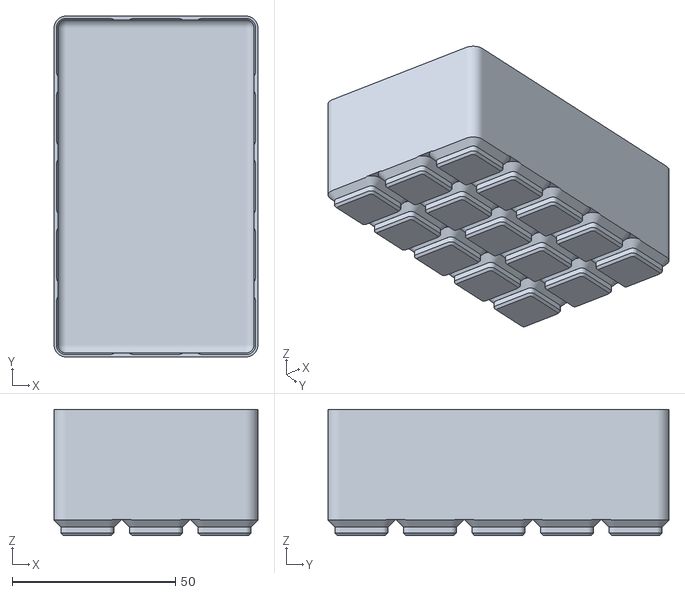
[picture p120: CAD file, 2026-06-07]
scad/gridfinity/stl/bin-3x5x10h.stl
62.5 x 104.5 x 38.7
