karyandrew/hutchfinity/scad/gridfinity/stl/bin-1x1x5h.stl

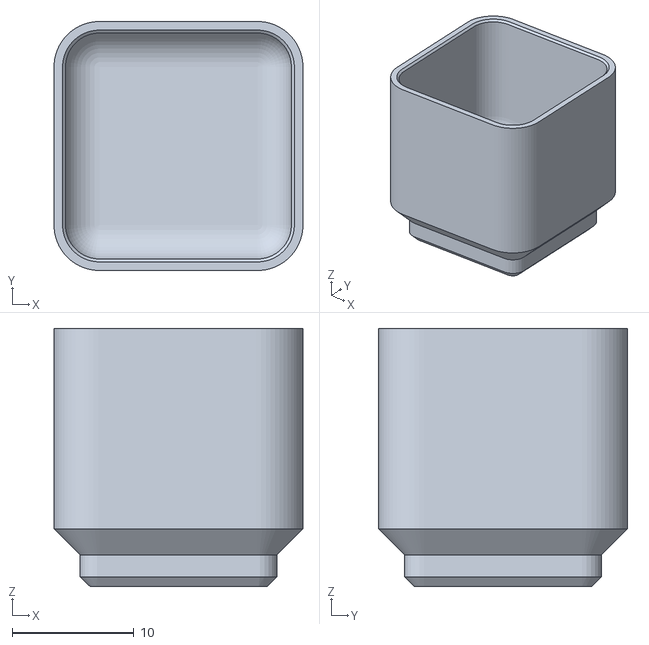
[picture p121: CAD file, 2026-06-07]
scad/gridfinity/stl/bin-1x1x5h.stl
20.5 x 20.5 x 21.2
