karyandrew/hutchfinity/scad/gridfinity/stl/bin-1x1x10h.stl

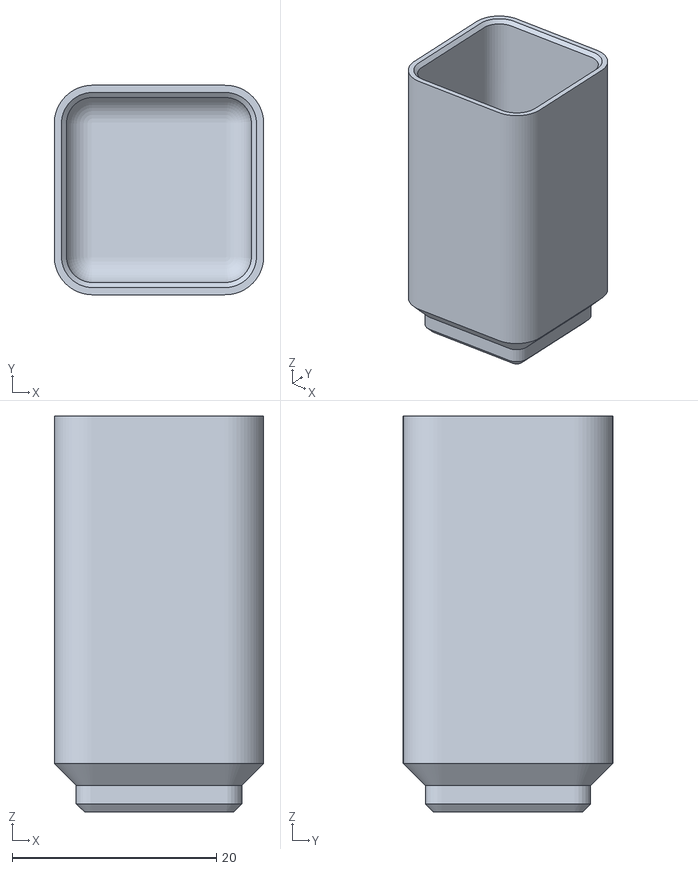
[picture p122: CAD file, 2026-06-07]
scad/gridfinity/stl/bin-1x1x10h.stl
20.5 x 20.5 x 38.7
