karyandrew/hutchfinity/scad/gridfinity/stl/bin-2x2x10h.stl

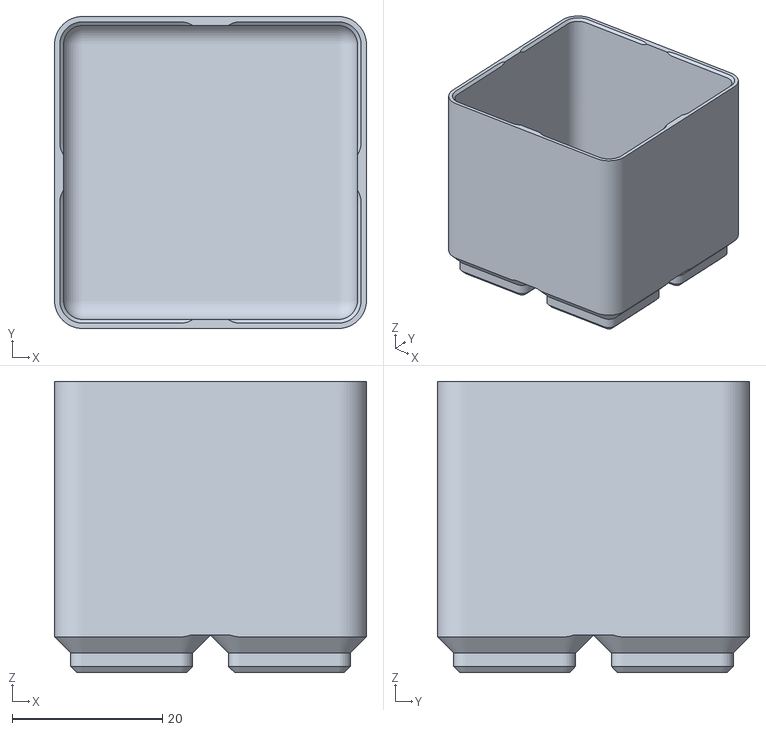
[picture p123: CAD file, 2026-06-07]
scad/gridfinity/stl/bin-2x2x10h.stl
41.5 x 41.5 x 38.7
