karyandrew/hutchfinity/scad/gridfinity/stl/baseplate-mini.stl

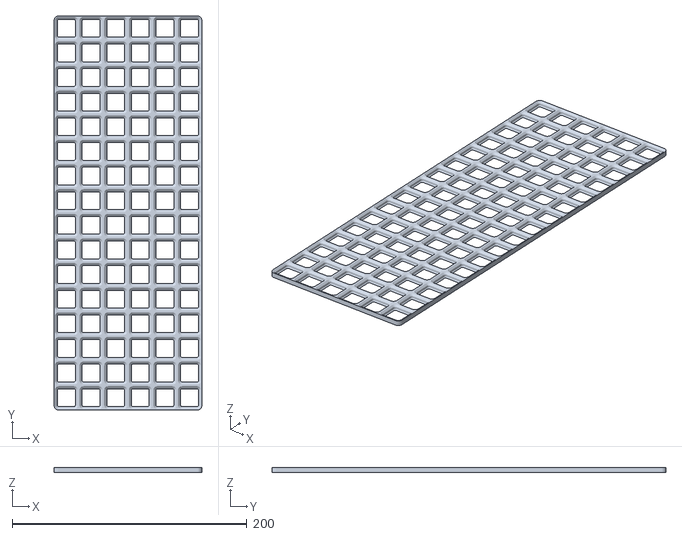
[picture p124: CAD file, 2026-06-07]
scad/gridfinity/stl/baseplate-mini.stl
126.0 x 336.0 x 4.00
