karyandrew/hutchfinity/scad/gridfinity/stl/bin-2x9x10h.stl

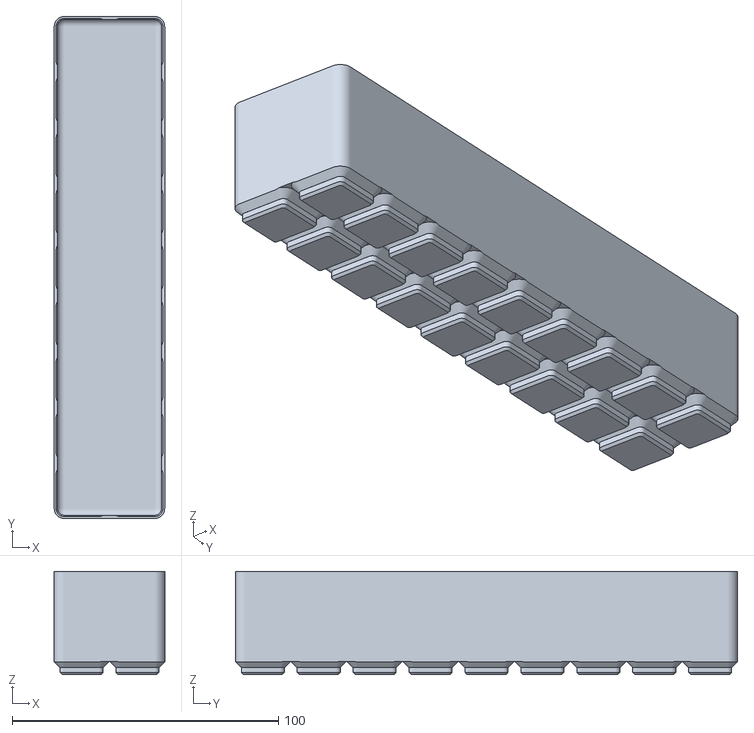
[picture p125: CAD file, 2026-06-07]
scad/gridfinity/stl/bin-2x9x10h.stl
41.5 x 188.5 x 38.7
