karyandrew/hutchfinity/scad/gridfinity/stl/bin-2x4x10h.stl

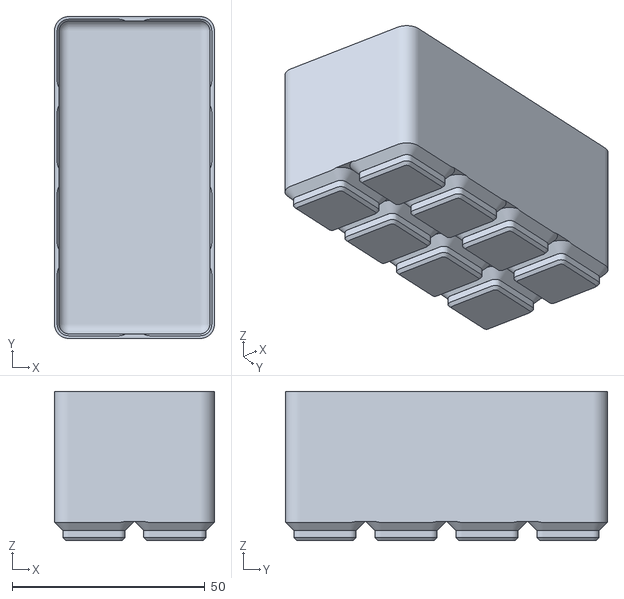
[picture p126: CAD file, 2026-06-07]
scad/gridfinity/stl/bin-2x4x10h.stl
41.5 x 83.5 x 38.7
