karyandrew/hutchfinity/scad/gridfinity/stl/bin-3x3x5h.stl

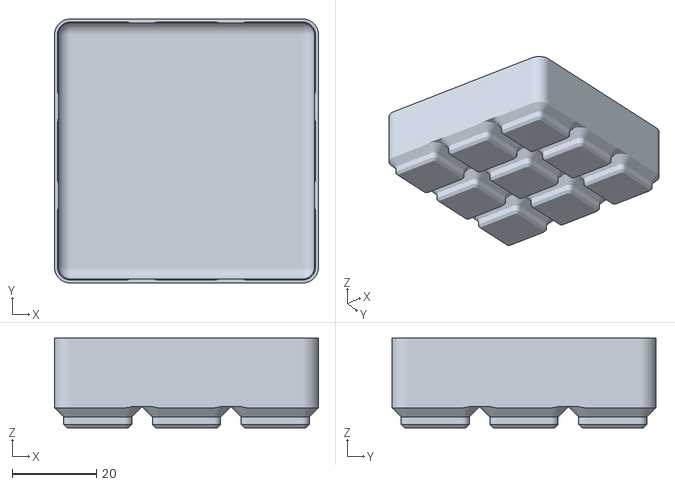
[picture p127: CAD file, 2026-06-07]
scad/gridfinity/stl/bin-3x3x5h.stl
62.5 x 62.5 x 21.2
