karyandrew/hutchfinity/scad/gridfinity/stl/bin-1x1x20h.stl

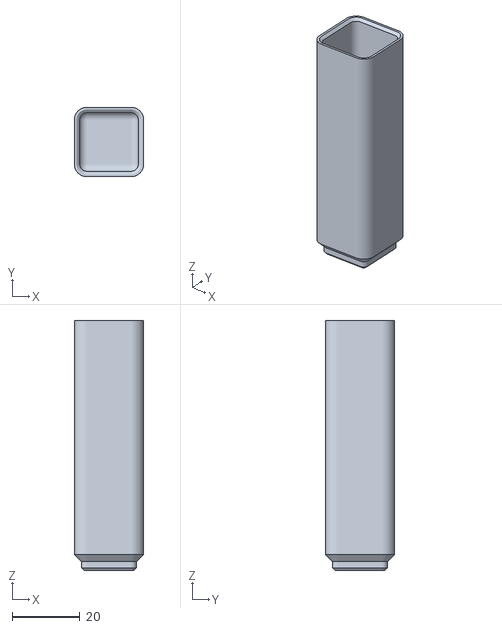
[picture p128: CAD file, 2026-06-07]
scad/gridfinity/stl/bin-1x1x20h.stl
20.5 x 20.5 x 73.7
