karyandrew/hutchfinity/scad/gridfinity/stl/bin-5x9x5h.stl

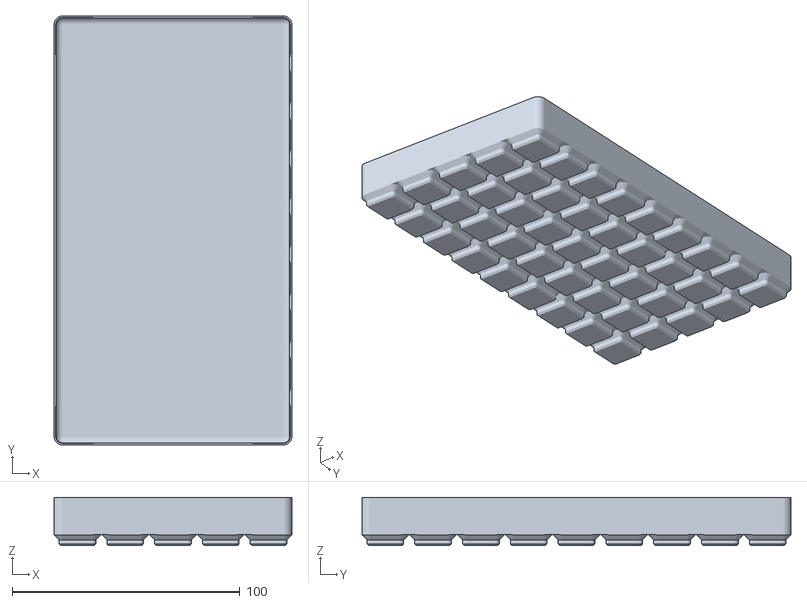
[picture p129: CAD file, 2026-06-07]
scad/gridfinity/stl/bin-5x9x5h.stl
104.5 x 188.5 x 21.2
