karyandrew/hutchfinity/scad/gridfinity/stl/bin-2x3x10h.stl

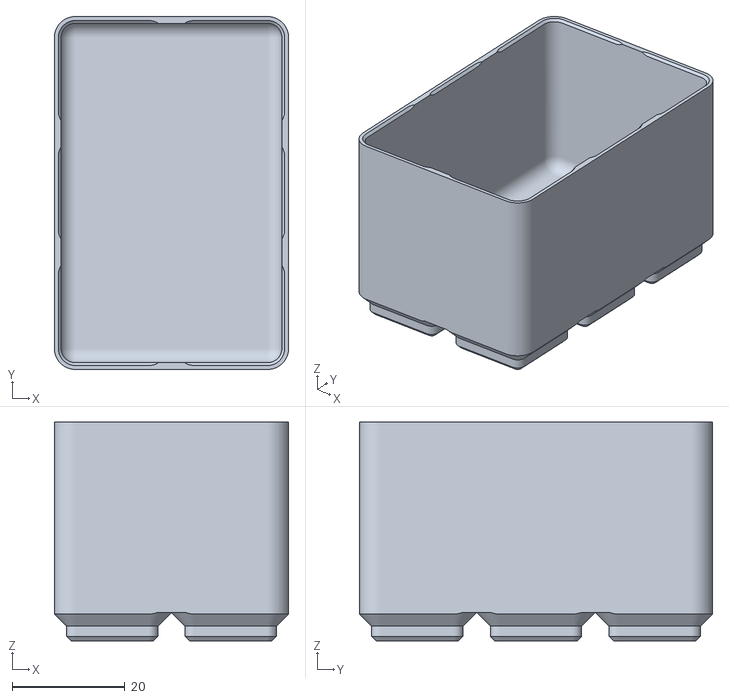
[picture p130: CAD file, 2026-06-07]
scad/gridfinity/stl/bin-2x3x10h.stl
41.5 x 62.5 x 38.7
