karyandrew/hutchfinity/scad/gridfinity/stl/bin-2x10x10h.stl

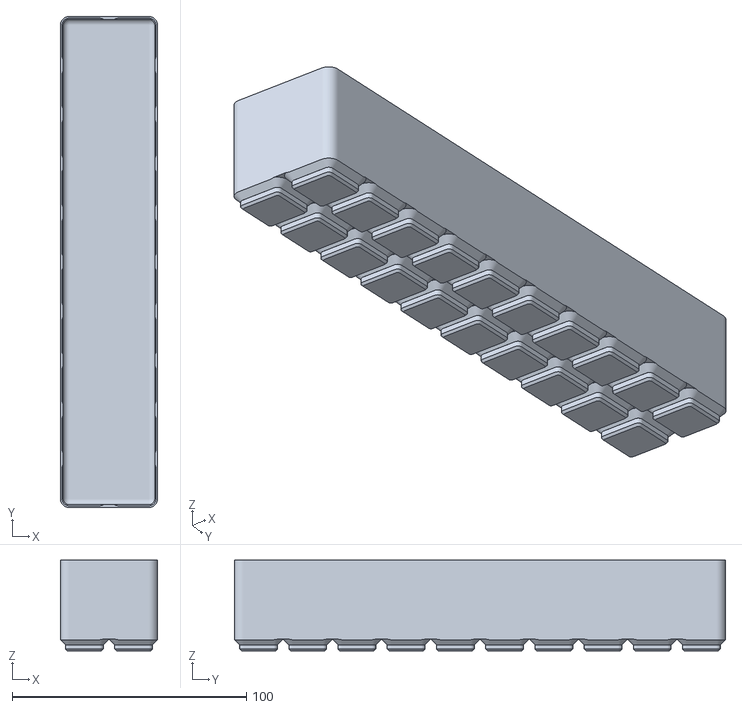
[picture p131: CAD file, 2026-06-07]
scad/gridfinity/stl/bin-2x10x10h.stl
41.5 x 209.5 x 38.7
