karyandrew/hutchfinity/scad/gridfinity/stl/bin-2x2x20h.stl

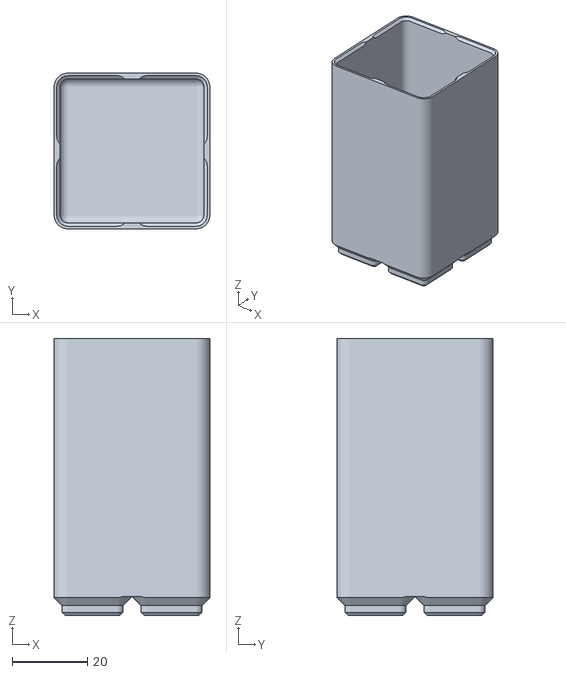
[picture p132: CAD file, 2026-06-07]
scad/gridfinity/stl/bin-2x2x20h.stl
41.5 x 41.5 x 73.7
